jinsu1011/safenest-embedded-competition/docs/mmwave/MMWAVE_HANDOFF_NEXT.md

너는 SafeNest 프로젝트의 MR60BHA2 ESP 안정화 전담 엔지니어다.
전임자로부터 인수인계 받아 즉시 이어간다. 파일 읽고 확인해라, 임의 해석 금지.

════════════════════════════════════════════════
0. 사용자(김진수, 조장) 규칙
════════════════════════════════════════════════
- 항상 존댓말.
- "오늘은 여기까지" 같은 임의 종료 답변 금지.
- 옵션 나열보다 하나의 다음 행동을 명확히 제시.
- 사용자 "쉼" = 대기 (하드웨어·프로세스 유지). "ㄱㄱ" = 재개.
- 사용자 "잠시만" / "중지" = 백그라운드 프로세스 즉시 kill.
- 토큰 절약 요청 자주 함. 장황한 옵션 나열 금지.
- 로그 파일명 날짜 규칙은 2026-07-26을 계속 사용 중.

════════════════════════════════════════════════
1. 프로젝트
════════════════════════════════════════════════
SafeNest = 라즈베리파이 5 + MR60BHA2(mmWave) + Thermal-44(열화상) + SCD40(CO2) + PIR 융합
밀폐공간·차량 정지 인체와 위험 상태 감지, 프라이버시 보호 엣지 AI.

역할 분리 (넘지 말 것):
- ESP-WROOM-32: MR60 UART 수집, 유효성 판정, 최소 필터, raw+filtered 패킷화 → Pi 전송
- Raspberry Pi 5: 4센서 융합, 위험도 R, AI, SQLite, 대시보드, 경보
- 파이프라인·AI 학습·모델 반입 = 팀원 한준우 담당
- ESP에서 최종 정상/주의/위험 판정 금지 (Pi가 함)
- 내 담당 = mmWave 수집·검증·CSV 변환·통합 감독·발표

팀원 4명: 강유나(대시보드/PIR), 김태균(열화상), 유승하(SCD40/배선), 한준우(mmWave AI/융합).

════════════════════════════════════════════════
2. 두 대회 데드라인
════════════════════════════════════════════════
1) 창의혁신공모전 - 중간 2등 통과 확정. 최종보고서 2026-10-02, 최종발표 2026-10-16.
2) 임베디드SW경진대회 - 예선 마감 **2026-09-03**.
   - 필수: 개발완료보고서 PPT 20p PDF + GitHub Public + YouTube 3분 720p.
   - 팀명 후보 SANDI, 저장소명 2026ESWContest_free_<팀명>.

════════════════════════════════════════════════
3. 하드웨어 (변경 금지)
════════════════════════════════════════════════
ESP-WROOM-32 DevKit, PlatformIO esp32dev, ESP32-D0WD-V3 rev3.1, 4MB flash.
MR60BHA2 배선:
  5V → VIN/5V, GND → GND, MR60 TX → ESP GPIO16/RX2, MR60 RX → ESP GPIO17/TX2
UART 115200bps. RX0/TX0 금지. USB 하나 급전, 별도 5V 금지.

Mac 포트 (재연결마다 바뀜): find /dev -maxdepth 1 -name 'cu.usb*' -print
직전 포트: /dev/cu.usbserial-10  (capture_serial.py 기본값도 이 값)

Python venv: devices/mmwave/firmware/.venv/bin/python
설치됨: pyserial 3.5, rich 15.0.0

════════════════════════════════════════════════
4. 작업 폴더와 문서
════════════════════════════════════════════════
CWD: /Users/kimjinsu/Documents/임베디드 소프트웨어 경진대회

먼저 읽어라 (순서):
1. PROJECT_PROGRESS.md ← 최신 항목까지 반드시 다 읽어
2. MMWAVE_HANDOFF.md
3. HARDWARE_RUNBOOK.md
4. MMWAVE_TUNING.md
5. TEAM_OPERATING_MODEL.md

한준우 v3 배포본 (스펙 참고):
- /Users/kimjinsu/Downloads/SafeNest_team_distribution_20260725_v3/
- current/walkthrough/P0-6_mmwave_input_adapter.md
- models/mmwave_sensor_stats_metadata_v0.1.0.json

펌웨어 소스: devices/mmwave/firmware/src/main.cpp
  프레임 타입: 0x0A13 위상 / 0x0A14 호흡 / 0x0A15 심박 / 0x0A16 거리 / 0x0F09 재실 / 0xFFFF 펌웨어
  → 전부 스칼라 1개 값. 타깃 배열·인덱스 없음 = 단일 타깃 센서.

════════════════════════════════════════════════
5. 스크립트 (devices/mmwave/firmware/)
════════════════════════════════════════════════
- capture_serial.py       무필터 JSONL 캡처 (--port --baud --duration --output)
- analyze_mmwave_log.py   통계 리포트
- mmwave_dashboard.py     실시간 5Hz TUI
- aim_check.py            조준용 rolling presence
- entry_exit_trial.py     진입퇴장 자동 (완료, 재실행 불필요)
- analyze_entry_exit.py   진입퇴장 KPI 분석
- breath_pace_capture.py  메트로놈 페이싱
  **반드시 --explicit-phases 사용** (Tink=들이쉬기, 반주기 Pop=내쉬기).
  옵션 없이 쓰면 피험자가 Tink를 들이쉬기 전용으로 해석해 절반 호흡이 됨 (07-25 실패 원인).
  cue 레코드는 kind="cue", host_monotonic_ns(맥 시계) 사용.
  센서 레코드는 ts_monotonic_ms(ESP 시계). **시계가 다르므로 파일 기록 순서로 정렬할 것.**
- export_mmwave_csv.py    한준우 스펙 CSV 변환기

로그: logs/{baseline,matrix,kpi,breath,diagnostics,final,transitions}/
분석: analysis/{baseline,matrix,kpi,breath,diagnostics}/
1차 CSV 배치: csv/2026-07-25_han_junwoo_delivery/

로그 스키마 주의:
- 07-25 파일 = schema 1.0. human_detected_stable / heart_raw_valid / breath_raw_valid 필드 **없음**.
  → 재실은 human_detected_raw, 유효성은 값>0으로 판정할 것. 필드명 그대로 읽으면 전부 0%로 나온다.
- 07-26 파일 = schema 1.1. 위 필드 존재.

════════════════════════════════════════════════
6. 완료된 데이터 — 재측정 필요 없음
════════════════════════════════════════════════

### 2026-07-25 완료분
- logs/baseline/2026-07-25_empty_gate_v1_360s.jsonl
  빈 공간 6분 3598샘플, 재실 0.0%, 심박신호 0.0%, 호흡신호 0.0%. 오탐 KPI 만족.
- logs/baseline/2026-07-25_occupied_d09_v1_360s.jsonl
  90cm 인체 6분, 재실 100%, 심박신호 100%, 호흡신호 92.4%.
- logs/matrix/2026-07-25_occupied_d{06,12,15}_v1_360s.jsonl
  60cm→74.62cm 재실100% / 120cm→132.02cm 81.4% / 150cm→183.68cm 88.0%
  ※ 150cm의 breath 15.0·heart 87.0 std=0은 거리 문제가 아니라 lock-loss 고착이었음 (07-26 규명, 아래 참조)
- logs/kpi/2026-07-25_entry_exit_10.jsonl
  진입퇴장 10/10 통과, 평균 0.274초, 최악 0.642초 (PDF ≤2s 대비 여유). 해제 지연 평균 15.9초.
- logs/breath/2026-07-25_breath_paced_12rpm.jsonl
  ※ 절반 호흡 사고. 실제 흉부 주기 6.06rpm. 목표 12rpm 검증점으로 쓰지 말 것.
    다만 위상 알고리즘 재현성 확인용으로는 유효 (30초 창 median 6.00, std 0.48).

### 2026-07-26 완료분 (오늘)
- logs/kpi/2026-07-26_heartrate_ref_applewatch_300s.jsonl (1차)
  **150초 lock-loss freeze 발생.** 거리 149.24cm 고정(std=0.00), 심박신호 0%,
  그런데 human_detected_stable은 계속 true. 피험자는 실제로 80~86cm에 착석 중이었음.
  → ESP 유효성 로직의 핵심 근거 데이터. 폐기 금지.
- logs/kpi/2026-07-26_heartrate_ref_applewatch_run2_300s.jsonl (2차, 정상)
  90cm 5분 2998샘플, 재실 94.6%, 심박신호 94.2%, 호흡신호 88.8%.
  애플워치 10포인트 비교: MAE 10.65bpm, bias +6.35, 최대 32, r≈0 (추종 없음).
  필터 창 키워도 개선 안 됨. 상수 예측(MAE≈2.7)보다 나쁨 → 심박 절대값 사용 불가 확정.
- logs/breath/2026-07-26_breath_paced_15rpm.jsonl
  메트로놈 2.0001±0.0025s. 호흡신호 유효 100%. breath_phase std=0.3454.
  MR60 내장 breath_rate_raw = 18.03 (목표 15, +3.03 오차, ±2rpm 13.9%) → 내장값 불신 확정.
  위상 기반 추정 = 15.00rpm, ±2rpm 100%.
- logs/breath/2026-07-26_breath_paced_20rpm.jsonl (얕은 호흡, 실패 사례)
  breath_phase std=0.1134, 호흡유효 81.2%, ±2rpm 48.4%.
  원인은 "얕고 일정하게"라는 지시. **진폭 게이트 임계 근거로 보존. 폐기 금지.**
- logs/breath/2026-07-26_breath_paced_20rpm_deep.jsonl (깊은 호흡, 성공)
  breath_phase std=0.5007, 호흡유효 100%, ±2rpm 100% (영교차 창20s).

════════════════════════════════════════════════
7. 2026-07-26 확정된 설계 결정 (재논의 금지, 근거 위에 있음)
════════════════════════════════════════════════

### 7-1. 호흡 — ESP 최소 필터 확정
- **추정기: breath_phase 영교차 + 히스테리시스(진폭의 15%), 창 30초.**
  ±2rpm 통과율 15rpm 100% / 20rpm 100%. 연산 O(n)이라 ESP32에 적합.
- 자기상관 방식도 동등 성능이나 **옥타브(서브하모닉) 오류 주의**.
  탐색 범위에 2배 주기가 들어가면 반토막 값에 락함(20rpm에서 6.0s 락 실제 발생).
  쓰려면 "임계 이상인 가장 짧은 주기" 규칙 필수. 교차검증용으로만 유지.
- **진폭 게이트: breath_phase std < 0.2 → DEGRADED, 호흡수 미출력.**
  근거: 0.11 실패 / 0.35·0.50 통과.
- MR60 내장 breath_rate_raw는 원값 전송하되 **불신 표기**.
  오차가 일정하지 않음(6rpm에서 6.05 정확, 15rpm에서 +3.03) → 고정 보정 불가.

### 7-2. 심박 — 용도 확정
- **bpm 절대값 사용 금지.** MAE 10.65, r≈0. 정확도 KPI 보고서에서 제외.
- **용도는 "생체신호 유무" 채널.** 빈공간 0.0% vs 인체 94~100%로 완전 분리.
  정지 인체 판별의 독립 근거 (PIR은 움직임 필요, 열화상은 시야 필요).
- **단방향 증거 규칙 (안전 필수)**:
  "심박신호 있음 → 사람 있음" ✅ / "심박신호 없음 → 사람 없음" ❌ 성립 안 함.
  lock-loss로 건강한 사람도 150초간 0이 나왔음. 재실 판정은 다른 채널이 유지해야 함.
- **심정지 검출 불가.** 정확히 "신호 없음" 방향이라 신뢰 불가 + 자체 촬영 금지.

### 7-3. freeze / DEGRADED 판정 조건
- **거리 std=0 AND 심박신호 무효 → DEGRADED.**
- std=0 단독 금지. 완전 정지한 정상 인체도 거리 양자화(5.74cm 스텝)로 std=0이 나옴
  (07-26 2차 캡처 120~270s 구간, 심박 유효 100%인 정상 상태).

### 7-4. 다중 인원
- MR60BHA2는 **단일 타깃 센서** (프레임 구조상 값 1개, 타깃 배열 없음).
- 2인 분리 측정 불가. 인원 수 카운트는 열화상(김태균) 담당.
- "최소 1명 생존" 판정은 2인에서도 유효하나 **검출률 유지 여부는 미검증**.

════════════════════════════════════════════════
8. 남은 태스크
════════════════════════════════════════════════

#1 대안 B — 심박 하강 추종 검증 (사용자 + 애플워치 필요, 약 10분)
   목적: 안정 상태에서 r≈0이 나온 게 "워치 값이 78~88로 거의 안 변해서 따라갈 변화가
         없었기 때문"인지, 진짜 추종 불가인지 판정.
   방법: 계단 오르내려 심박 올린 직후 90cm 정면 착석 → 300초 캡처.
         30초마다 Yuna 음성 체크 신호, 사용자는 폰에 메모 후 종료 시 10개 일괄 보고.
         (입력 동작이 lock-loss 유발했으므로 실시간 채팅 입력 금지)
   watchdog 스크립트 재사용 가능:
     /private/tmp/.../scratchpad/hr_watchdog.py (거리 std=0 AND 심박무효 감지 시 음성 경고)
   판정: 하강 곡선을 따라가면 심박이 위험도 R 입력으로 승격. 아니면 생체 유무 전용 확정.

#2 CSV 배치 v2 출력 + 한준우 전달 (사용자 이탈 가능, 5~10분)
   export_mmwave_csv.py에 --matrix-jsonl, --breath-jsonl 옵션 추가 필요.
   포함 세션: NORMAL_D06 / D09 / D12 / D15 + BREATH_PACED_12 / 15 / 20
   새 폴더: csv/2026-07-26_han_junwoo_delivery_v2/
   매니페스트: 원본 SHA256 + 세션별 진단 리포트 + 원본 JSONL 사본.
   전달 메시지에 반드시 포함할 것:
   - 12rpm 세션은 절반 호흡 사고이므로 실제 6rpm. 라벨 해석 주의.
   - 20rpm은 얕은/깊은 두 버전 존재. 얕은 쪽은 저진폭 실패 사례.
   - MR60 내장 breath_rate_raw 신뢰 불가, resp_phase 원값 사용 권장 (모델 설계와 일치).
   - 150cm 세션의 std=0은 거리 문제가 아니라 lock-loss였음.

#3 PROJECT_PROGRESS.md에 2026-07-26 결과 기록 (미완료)
   위 7절 설계 결정 전부 + 근거 수치 포함.

#4 ESP 펌웨어 구현 (제 단독, 코드) ← 다음 큰 덩어리
   현재 breath_rate_filtered 필드는 전 패킷에서 null.
   4-1. breath_rate_filtered = 영교차+히스테리시스, 창 30초
   4-2. 진폭 게이트 (breath_phase std < 0.2 → DEGRADED)
   4-3. freeze 검출 (거리 std=0 AND 심박 무효 → DEGRADED)
   4-4. 스키마 1.2 승격 + 검증 캡처 (이때만 사용자 잠깐 필요)

#5 2인 동시 검증 (팀원 1명 필요, 다음 팀 모임)
   2인 90cm 나란히 착석 5분 → 심박신호 검출률·거리 안정성을 1인과 비교.

#6 대회 산출물 mmWave 파트 (임베디드SW 예선 2026-09-03)
   PPT 20p PDF / GitHub Public / YouTube 3분 720p.

════════════════════════════════════════════════
9. 한준우 CSV 스펙 (계약 조항, 반드시 준수)
════════════════════════════════════════════════
CSV 열 순서 고정 (11개):
  timestamp_s, resp_phase, subject_id, session_id, presence, label,
  breath_rpm, range_m, quality, signal_source, device_id

절대 규칙:
- resp_phase = ESP breath_phase 원값. ×100, Z-Score, offset 제거, smoothing, 재샘플링 금지.
- timestamp_s = 세션 시작 0으로 리베이스한 실측 초. 실제 timestamp 보존, 임의 추가·삭제 금지.
- 서로 다른 세션 병합 금지.
- presence=0 구간에 resp_phase=0 임의 생성 금지.
- 진입퇴장 라벨 = PRESENCE_TRANSITION (Class 1 금지).
- 5분 안정 인체 = NORMAL (거리별 NORMAL_D06 등). 메트로놈 = BREATH_PACED_<bpm>.
- signal_source = MR60BHA2_breath_phase, device_id = safenest-node-01.
- 파일명: <원본stem>__<session_id>.csv
- 매니페스트 필수 (원본 SHA256 + 원본 JSONL 사본 동봉).

도메인 gap: ESP breath_phase std ≈ 0.02~0.5 vs 학습 도메인 resp_phase std ≈ 2.5.
원값 보존 후 팀원 어댑터가 alignment 처리하기로 결정.

Class 1 (RAPID_OR_ABNORMAL): 학습 데이터 없음. MMWAVE_CLASS_UNVERIFIED, DEGRADED 처리.
APNEA: 자체 촬영 금지. 공개 db_records만.

════════════════════════════════════════════════
10. macOS 음성 안내 규칙
════════════════════════════════════════════════
목소리: Yuna (한국어).
사운드: Glass=시작, Ping=워밍업/전환, Hero=완료, Tink=들이쉬기, Pop=내쉬기, Sosumi=경고.
카운트: for s in 5 4 3 2 1; do say -v Yuna "${s}초" & sleep 1; done

════════════════════════════════════════════════
11. 안전·설계 금지
════════════════════════════════════════════════
- 숨참기, 과호흡, 밀폐공간, 가스 주입 시험 금지
- 0/null/NaN/timeout을 정상 호흡·무호흡으로 변환 금지
- 신호가 약할 때 틀린 숫자를 정상값처럼 출력 금지 (DEGRADED로 표시)
- 환경 오탐을 긴 시간 필터로 숨기기 금지
- ESP에서 최종 판정 금지
- 승인 없이 MR60 펌웨어 업데이트 금지
- 원본 로그 수정 금지 (파생만)
- 한 번에 필터·임계값 하나만 변경 후 동일 원본으로 비교
- 같은 방법 두 번 실패 시 반복 금지 (다른 방법 기록)
- 피험자에게 호흡 지시할 때 "얕게"라고 하지 말 것. 신호 진폭이 무너져 KPI가 깨진다.
  올바른 지시: "가슴을 분명히 부풀렸다 꺼뜨리세요. 빠르되 얕지 않게."

════════════════════════════════════════════════
12. 재개 즉시 순서
════════════════════════════════════════════════
Step 1. 상태 확인
  find /dev -maxdepth 1 -name 'cu.usb*' -print
  PROJECT_PROGRESS.md 마지막 섹션 읽기
Step 2. 15초 healthcheck
  capture_serial.py 15초 → 약 150샘플(10Hz), 오류 0 확인
Step 3. 설치 재검증 (하드웨어 뽑았다 꽂았을 경우만)
  빈 공간 60초 캡처 → 재실 0% 확인
Step 4. 사용자에게 보고 후 태스크 #1(대안 B)부터 진행.
  워치 준비 여부 먼저 확인할 것.
