jinsu1011/safenest-embedded-competition/docs/mmwave/MMWAVE_MASTER.md

# SafeNest mmWave 총정리 (2026-08-01 기준)

이 문서 하나로 인수인계가 끝나도록 작성했다. 다른 문서를 안 읽어도 이어서 작업할 수 있다.
`MMWAVE_HANDOFF_NEXT.md`와 내용이 겹치면 **이 문서가 우선**한다.

---

## 1. 프로젝트가 뭔가

**SafeNest** = 밀폐공간·정지 차량 안에서 **의식을 잃고 움직이지 않는 사람**을 찾아내는 엣지 AI 장치.
카메라를 쓰지 않아 프라이버시를 보호하는 것이 정체성이다.

센서 4종을 융합한다.

| 센서 | 역할 | 담당 |
|---|---|---|
| **MR60BHA2 (mmWave)** | 정지 인체의 호흡·생체신호 | **김진수 (나)** |
| Thermal-44 (열화상) | 인원 수·위치 | 김태균 |
| SCD40 (CO2) | 공간 환경 위험 | 유승하 |
| PIR | 움직임 | 강유나 |
| 융합·AI·대시보드 | 위험도 R 산출 | 한준우, 강유나 |

연산은 **Raspberry Pi 5**에서, 센서 수집은 **ESP-WROOM-32**에서 한다.

### 왜 mmWave가 핵심인가
움직이는 사람은 PIR로도 잡는다. 문제는 **쓰러져서 안 움직이는 사람**이다.
- PIR → 움직여야 감지. 못 잡음.
- 열화상 → 담요·시트·시야 가림에 약함.
- CO2 → 공간 전체 값이라 개인 특정 불가.
- **mmWave → 정지해 있어도 흉부의 호흡 미세 움직임을 잡는다.**

즉 mmWave가 이 프로젝트에서 **가장 어려운 문제를 맡은 센서**다.

### 역할 경계 (넘지 말 것)
- **ESP-WROOM-32**: MR60 UART 수집 → 유효성 판정 → 최소 필터 → raw+filtered 패킷화 → Pi 전송
- **Raspberry Pi 5**: 4센서 융합, 위험도 R, AI 추론, SQLite, 대시보드, 경보
- **ESP에서 "정상/주의/위험" 최종 판정 금지.** 판정은 Pi가 한다.
- AI 학습·모델 반입은 한준우 담당. 내가 하지 않는다.
- 내 담당 = mmWave 수집·검증·CSV 변환·통합 감독·발표

---

## 2. 하드웨어와 실행 환경

```
ESP-WROOM-32 DevKit (ESP32-D0WD-V3 rev3.1, 4MB flash, PlatformIO esp32dev)
MR60BHA2 배선:
  5V  → VIN/5V
  GND → GND
  MR60 TX → ESP GPIO16 (RX2)
  MR60 RX → ESP GPIO17 (TX2)
UART 115200bps. RX0/TX0 사용 금지. USB 하나로 급전, 별도 5V 금지.
```

- 작업 폴더: `/Users/kimjinsu/Documents/임베디드 소프트웨어 경진대회`
- GitHub: `jinsu1011/safenest-embedded-competition` (**private**), 브랜치 `codex/mmwave-phase-integration`
- Python: `devices/mmwave/firmware/.venv/bin/python` (pyserial, rich)
- 시리얼 포트는 **재연결마다 바뀐다**: `find /dev -maxdepth 1 -name 'cu.usb*' -print`
  - 최근 값 `/dev/cu.usbserial-10`
- 펌웨어 소스: `devices/mmwave/firmware/src/main.cpp`
- 샘플레이트 약 **10Hz**

### MR60BHA2 UART 프레임 (main.cpp:15~21)
`0x0A13` 위상 / `0x0A14` 호흡수 / `0x0A15` 심박수 / `0x0A16` 거리 / `0x0F09` 재실 / `0xFFFF` 펌웨어

**전부 값 1개짜리 스칼라다. 타깃 배열도 인덱스도 없다 → 단일 타깃 센서.**

---

## 3. 지금까지 한 것 (전부 완료, 재측정 불필요)

원본 로그는 전부 `devices/mmwave/firmware/logs/` 에 있고 GitHub에 푸시돼 있다.
**원본 수정 금지. 파생 파일만 만든다.**

### 3-1. 환경 검증
| 세션 | 파일 | 결과 |
|---|---|---|
| 빈 공간 6분 | `baseline/2026-07-25_empty_gate_v1_360s.jsonl` | 3598샘플, 재실 **0.0%**, 심박신호 0.0%, 호흡신호 0.0% → 오탐 KPI 통과 |
| 90cm 인체 6분 | `baseline/2026-07-25_occupied_d09_v1_360s.jsonl` | 재실 100%, 심박신호 100%, 호흡신호 92.4% |

### 3-2. 거리 매트릭스
`matrix/2026-07-25_occupied_d{06,12,15}_v1_360s.jsonl`

| 안내 거리 | 실측 | 재실 | 판정 |
|---|---|-----|-----|
| 60cm | 74.62cm | 100% | 최적 |
| 90cm | 97.58cm | 100% | 최적 |
| 120cm | 132.02cm | 81.4% | KPI 미달 |
| 150cm | 183.68cm | 88.0% | 측정 실패 |

**최적 흉부 거리 = 60~100cm.**
※ 150cm의 `std=0` 상수값은 원래 "거리가 멀어 실패"로 기록됐으나, 2026-08-01에 **거리 문제가 아니라 lock-loss 고착**임이 밝혀졌다 (5-3 참조).

### 3-3. 진입/퇴장 KPI — 통과
`kpi/2026-07-25_entry_exit_10.jsonl` (센서 4215 + 비프 20)
- **감지 10/10 통과. 평균 0.274초, 최악 0.642초** (요구 ≤2초 대비 3배 여유)
- 해제 지연은 평균 15.9초 (MR60 hysteresis 추정, 우선순위 낮음)

### 3-4. 심박 정확도 대조 (애플워치 기준) — 2026-08-01
| 파일 | 내용 |
|---|---|
| `kpi/2026-07-26_heartrate_ref_applewatch_300s.jsonl` | 1차. **150초 lock-loss freeze 발생** |
| `kpi/2026-07-26_heartrate_ref_applewatch_run2_300s.jsonl` | 2차. 정상. 2998샘플, 재실 94.6%, 심박신호 94.2%, 호흡신호 88.8% |

2차에서 워치 10포인트와 대조한 결과:
- **MAE 10.65bpm, bias +6.35, 최대 오차 32bpm, 상관계수 r ≈ 0**
- 중앙값 필터 창을 ±5s→±45s로 9배 키워도 bias는 +6.35→+5.00으로 거의 안 줄었다.
- 워치 std가 3.38이라 **"그냥 평균값 79.6을 상수로 찍는 예측"의 MAE가 약 2.7**이다.
  MR60을 필터링하고 오프셋 보정해도 **4.20** — **아무것도 안 재는 것보다 나쁘다.**
- → **심박 bpm 절대값은 회귀·보정·캘리브레이션으로 못 살린다. 확정.**

### 3-5. 메트로놈 호흡 시험 — 2026-08-01
`breath_pace_capture.py --explicit-phases` 사용 (Tink=들이쉬기, 반주기 Pop=내쉬기).

| 파일 | 목표 | breath_phase 진폭(std) | 호흡유효 | 비고 |
|---|-----|---|---|---|
| `breath/2026-07-25_breath_paced_12rpm.jsonl` | 12rpm | — | 67.8% | **절반 호흡 사고. 실제 6.06rpm** |
| `breath/2026-07-26_breath_paced_15rpm.jsonl` | 15rpm | **0.3454** | 100% | 성공 |
| `breath/2026-07-26_breath_paced_20rpm.jsonl` | 20rpm | **0.1134** | 81.2% | **얕은 호흡 실패 사례** |
| `breath/2026-07-26_breath_paced_20rpm_deep.jsonl` | 20rpm | **0.5007** | 100% | 성공 |

메트로놈 자체 정확도는 완벽했다 (15rpm에서 2.0001±0.0025초).

---

## 4. 확정된 설계 결정 — **재논의 금지, 근거는 위 데이터**

### 4-1. 호흡 — ESP 최소 필터 (핵심 성과)

**MR60 내장 `breath_rate_raw`를 버리고, `breath_phase` 원신호에서 직접 호흡수를 계산한다.**

`breath_phase` 자기상관으로 실제 흉부 주기를 재보니 메트로놈과 정확히 일치했다.
즉 **원신호는 정확한데 MR60의 내장 추정기가 틀린다.**

| 추정 방식 | 15rpm | 20rpm(깊은) | 결과 |
|---|---|---|---|
| MR60 내장 breath_rate_raw | 18.03 (오차 +3.03) | — | **±2rpm 통과율 13.9%** |
| **영교차 + 히스테리시스, 창 30초** | 15.30 | 20.17 | **±2rpm 100% / 100%** |
| 자기상관 + 옥타브 보정, 창 30초 | 14.96 | 19.97 | ±2rpm 100% / 99.3% |

**채택: 영교차 + 히스테리시스(진폭의 15%), 창 30초.**
연산량이 O(n)이라 ESP32에 적합하다. 자기상관은 동등 성능이지만 수십 배 무겁고 옥타브 오류 위험이 있어 교차검증용으로만 남긴다.

**진폭 게이트: `breath_phase` std < 0.2 → DEGRADED, 호흡수 미출력.**
근거: 0.11에서 실패(±2rpm 48.4%), 0.35·0.50에서 통과(100%).
신호가 약할 때 틀린 숫자를 정상값처럼 내보내는 것은 안전 규칙 위반이다.

**MR60 내장값은 원값 그대로 전송하되 "불신" 표기.**
오차가 일정하지 않다 — 6rpm에서는 6.05로 정확했는데 15rpm에서는 +3.03이었다. **고정 오프셋 보정이 불가능하다.**

### 4-2. 심박 — 용도 재정의

**bpm 절대값 사용 금지.** 보고서에서 심박 정확도 KPI를 뺀다.

**대신 "생체신호 유무" 채널로 쓴다.** 이건 데이터로 완전히 증명됐다.

| 세션 | 심박신호 검출률 |
|---|---|
| 빈 공간 6분 (3598샘플) | **0.0%** |
| 인체 90cm (2026-07-25) | **100.0%** |
| 인체 90cm (2026-08-01) | **94.2%** |

무인 3598샘플에서 오탐 **0건**. 완전히 분리된다.
→ **정지한 사람을 찾아내는 독립 근거**로 쓴다. 프로젝트 주제와 정확히 맞는 역할이다.

#### ⚠️ 단방향 증거 규칙 (안전 필수, 반드시 지킬 것)
- **"심박신호 있음 → 사람 있음"** ✅ 성립
- **"심박신호 없음 → 사람 없음"** ❌ **성립하지 않는다**

1차 캡처에서 **건강한 사람이 앉아 있는데도 150초 동안 신호가 0**이었다 (lock-loss).
이 방향으로 판정하면 사람을 놓친다. **재실 판정은 거리·호흡·PIR·열화상이 유지해야 한다.**

같은 이유로 **심정지 검출은 불가능하다.** 심정지는 정확히 "신호 없음" 방향인데, 그게 우리가 신뢰할 수 없다고 증명한 유일한 방향이다. 게다가 심정지는 자체 촬영이 금지돼 검증 데이터를 만들 수도 없다.

### 4-3. freeze / DEGRADED 판정

**조건: 거리 std=0 AND 심박신호 무효 — 두 개 동시 성립.**

`std=0` 단독으로 걸면 안 된다. 완전히 정지한 **정상** 인체도 거리 양자화(5.74cm 스텝) 때문에 std=0이 나온다 (2026-08-01 2차 캡처 120~270초 구간, 심박 유효 100%인 정상 상태).

### 4-4. 다중 인원

**MR60BHA2는 단일 타깃 센서다** (프레임이 전부 스칼라 1개, 타깃 배열 없음).
- 2인 분리 측정 불가. 사람별 개별 심박·호흡 불가. 인원 수 카운트 불가.
- **인원 수는 열화상(김태균)이 담당** — 설계상 이미 역할이 분리돼 있어 구멍이 아니다.
- "최소 1명 생존" 판정은 2인에서도 성립하나, **검출률이 유지되는지는 미검증** (남은 작업 #5).

---

## 5. 겪은 실패와 함정 — **같은 실수 반복 금지**

### 5-1. 절반 호흡 사고 (2026-07-25 12rpm)
메트로놈은 완벽했는데 센서가 5.63rpm을 읽었다. 목표 12rpm의 정확히 절반이었다.
원인은 센서가 아니라 **신호 해석**이었다. Tink를 "들이쉬기 신호"로만 듣고 다음 Tink에 내쉬어서 한 호흡에 10초를 썼다.
→ **`breath_pace_capture.py`는 반드시 `--explicit-phases`로 실행할 것.** (Tink=들이쉬기, 반주기 Pop=내쉬기)
→ 12rpm 세션은 **실제 6.06rpm**이므로 12rpm 검증점으로 쓰면 안 된다.

### 5-2. "얕게 쉬세요"라는 지시가 KPI를 깨뜨림
20rpm 1차에서 내가 "얕고 일정하게"라고 지시했다. 얕게 쉬면 흉부 변위가 작아져 신호 진폭이 0.1134까지 떨어졌고(정상 0.35~0.50) KPI가 48.4%로 무너졌다.
같은 20rpm을 **"가슴을 분명히 부풀렸다 꺼뜨리세요"** 로 다시 찍으니 진폭 0.5007, KPI 100%가 나왔다.
→ **피험자에게 "얕게"라고 지시하지 말 것.** 올바른 지시: "빠르되 얕지 않게, 가슴이 분명히 움직이게."

### 5-3. lock-loss freeze — 거리 문제가 아니었다
1차 심박 캡처에서 30초~180초 동안 거리가 **149.24cm에 완전 고정(std=0.00)**, 심박신호 0%였다. 피험자는 계속 80~86cm에 앉아 있었다.
이것은 2026-07-25 "150cm 측정 실패"와 **동일한 시그니처**다. 즉 **거리와 무관한 lock-loss 고착**이다. 어제 결론이 틀렸다.
더 심각한 건 그 150초 동안 `human_detected_stable`이 계속 **true**였다는 점이다 — ESP가 쓰레기 값을 재실 YES로 Pi에 넘긴다.
→ 이것이 4-3 판정 로직이 필요한 이유다. **이 로그는 폐기 금지.**
→ 움직임(채팅 입력)이 방아쇠로 추정된다. 캡처 중 피험자가 타이핑하지 않게 할 것.

### 5-4. 자기상관 옥타브(서브하모닉) 오류
20rpm에서 자기상관이 **6.000초(2배 주기)** 에 락해 10rpm을 출력했다. 실제는 3.0초/20rpm.
15rpm에서 통과한 건 알고리즘이 옳아서가 아니라 2배 주기 8.0초가 탐색 범위(상한 7.5초) 밖이라 **운이 좋았던 것**이다.
→ 자기상관을 쓸 거면 최대값이 아니라 **"임계(최대값의 85%) 이상인 가장 짧은 주기"** 를 골라야 한다.

### 5-5. 로그 스키마가 2종이다
- **2026-07-25 파일 = schema 1.0**: `human_detected_stable`, `heart_raw_valid`, `breath_raw_valid` 필드가 **없다**.
  그대로 읽으면 **전부 0%로 나온다**(실제로 한 번 잘못 계산했다). `human_detected_raw` + 값>0 으로 판정할 것.
- **2026-07-26 이후 = schema 1.1**: 위 필드 존재.

### 5-6. 시계가 2종이다
- cue 레코드(`kind="cue"`)는 `host_monotonic_ns` — **맥 시계**
- 센서 레코드는 `ts_monotonic_ms` — **ESP 시계**
- 서로 변환 불가. **파일에 기록된 순서로 정렬**해야 한다. `analysis_tools/`의 모든 스크립트가 이 방식을 쓴다.

---

## 6. 남은 작업 (우선순위 순)

| # | 작업 | 소요 | 사람 필요? | 하드웨어 필요? |
|---|---|---|---|---|
| 1 | **ESP 펌웨어 구현** | 큼 | 아니오 | 검증 때만 |
| 2 | CSV 배치 v2 + 한준우 전달 | 5~10분 | 아니오 | 아니오 |
| 3 | PROJECT_PROGRESS.md 기록 | 짧음 | 아니오 | 아니오 |
| 4 | 2026-07-28 로그 중복 확인 | 짧음 | 아니오 | 아니오 |
| 5 | 심박 하강 추종 검증 (선택) | 10분 | **예 + 애플워치** | 예 |
| 6 | 2인 동시 검증 | 10분 | **팀원 1명** | 예 |
| 7 | 대회 산출물 | 큼 | 팀 전체 | 일부 |

### #1 ESP 펌웨어 구현 ← **다음 큰 덩어리**
현재 `breath_rate_filtered` 필드는 **전 패킷에서 `null`** 이다. 설계만 확정됐고 코드가 없다.
1. `breath_rate_filtered` = breath_phase 영교차 + 히스테리시스(15%), 창 30초
2. 진폭 게이트: `breath_phase` std < 0.2 → DEGRADED
3. freeze 검출: 거리 std=0 AND 심박 무효 → DEGRADED
4. 패킷 스키마 **1.2**로 승격 + 검증 캡처 (이때만 사용자·하드웨어 필요)

참고 구현: `analysis_tools/phase_rate_zerocross.py` 의 `zc_rate()` 를 C++로 옮기면 된다.

### #2 CSV 배치 v2
`export_mmwave_csv.py`에 `--matrix-jsonl`, `--breath-jsonl` 옵션 추가 필요.
포함 세션: NORMAL_D06 / D09 / D12 / D15 + BREATH_PACED_12 / 15 / 20
출력 폴더: `csv/2026-07-26_han_junwoo_delivery_v2/`
매니페스트에 원본 SHA256 + 세션별 진단 + 원본 JSONL 사본 동봉.

**한준우에게 반드시 전달할 내용:**
- 12rpm 세션은 절반 호흡 사고라 **실제 6rpm**이다. 라벨 해석 주의.
- 20rpm은 얕은/깊은 두 버전이 있다. 얕은 쪽은 저진폭 실패 사례다.
- **MR60 내장 `breath_rate_raw`는 신뢰 불가.** `resp_phase` 원값을 쓰는 모델 설계가 옳다.
- 150cm 세션의 std=0은 거리 문제가 아니라 lock-loss였다.

### #4 2026-07-28 로그 중복 확인
`logs/breath/2026-07-28_breath_paced_*` 에 12rpm/15rpm explicit 재시도 로그가 있다.
내가 인수인계받지 못한 다른 세션의 작업이다. 2026-08-01 작업과 중복인지 확인하고 어느 쪽이 유효한지 정리할 것.

### #5 심박 하강 추종 검증 (선택)
안정 상태에서 r≈0이 나온 이유가 **워치 값이 78~88로 거의 안 변해 따라갈 변화가 없었기 때문**일 수 있다.
계단 운동으로 심박을 올린 뒤 90cm 착석 5분 캡처 → 110→80 하강 곡선을 MR60이 따라가는지 본다.
- 따라가면 → 심박이 위험도 R의 정식 입력으로 승격
- 아니면 → 생체 유무 전용으로 확정 (근거 2배)

**주의**: 캡처 중 피험자가 채팅에 타이핑하면 lock-loss가 유발된다(5-3). 폰에 메모했다가 끝나고 일괄 보고하게 할 것.
`analysis_tools/freeze_watchdog.py`를 동시에 돌리면 고착을 실시간 음성 경고해준다.

---

## 7. 대회 일정

| 대회 | 상태 | 마감 |
|---|---|---|
| 창의혁신공모전 | 중간 **2등 통과 확정** | 최종보고서 **2026-10-02** / 발표 **2026-10-16** |
| 임베디드SW경진대회 | 예선 준비 중 | **2026-09-03** |

**임베디드SW 예선 제출물 (필수 3종)**
1. 개발완료보고서 PPT 20페이지 → PDF
2. GitHub **Public** 저장소 (현재는 private) — 이름 규칙 `2026ESWContest_free_<팀명>`, 팀명 후보 **SANDI**
3. YouTube 3분 720p 영상

발표는 김진수(나) 담당.

---

## 8. 한준우 CSV 계약 스펙 (반드시 준수)

열 순서 고정 (11개):
```
timestamp_s, resp_phase, subject_id, session_id, presence, label,
breath_rpm, range_m, quality, signal_source, device_id
```

**절대 규칙**
- `resp_phase` = ESP `breath_phase` **원값**. ×100, Z-Score, offset 제거, smoothing, 재샘플링 **전부 금지**.
- `timestamp_s` = 세션 시작을 0으로 리베이스한 실측 초. 실제 timestamp 보존, 임의 추가·삭제 금지.
- 서로 다른 세션 **병합 금지**.
- `presence=0` 구간에 `resp_phase=0`을 임의 생성 금지 (원값 그대로).
- 라벨: 진입퇴장 = `PRESENCE_TRANSITION` (Class 1 금지) / 5분 안정 인체 = `NORMAL`(거리별 `NORMAL_D06` 등) / 메트로놈 = `BREATH_PACED_<bpm>`
- `signal_source` = `MR60BHA2_breath_phase`, `device_id` = `safenest-node-01`
- 파일명: `<원본stem>__<session_id>.csv`
- 매니페스트 필수 (원본 SHA256 + 원본 JSONL 사본 동봉)

**알려진 도메인 gap**: ESP `breath_phase` std ≈ 0.02~0.5 vs 학습 도메인 `resp_phase` std ≈ 2.5.
원값을 보존하고 **팀원 어댑터가 alignment를 처리**하기로 결정했다.

**Class 1 (RAPID_OR_ABNORMAL)**: 학습 데이터 없음 → `MMWAVE_CLASS_UNVERIFIED`, DEGRADED 처리.
**APNEA**: 자체 촬영 금지(안전 규칙). 공개 db_records만 사용.

---

## 9. 안전·설계 금지 사항

- 숨참기, 과호흡, 밀폐공간, 가스 주입 시험 **금지**
- 0/null/NaN/timeout을 정상 호흡이나 무호흡으로 변환 **금지**
- 신호가 약할 때 틀린 숫자를 정상값처럼 출력 **금지** (DEGRADED로 표시할 것)
- 환경 오탐을 긴 시간 필터로 숨기기 **금지**
- ESP에서 최종 판정 **금지**
- 승인 없이 MR60 펌웨어 업데이트 **금지**
- 원본 로그 수정 **금지** (파생 파일만)
- 한 번에 필터·임계값 **하나만** 변경 후 동일 원본으로 비교
- 같은 방법 두 번 실패하면 반복 금지 (다른 방법을 기록할 것)
- 피험자에게 **"얕게 쉬세요"라고 지시 금지** (5-2 참조)

---

## 10. 분석 도구 — `devices/mmwave/firmware/analysis_tools/`

하드웨어 없이 로그만으로 위 결론을 전부 재현할 수 있다. 표준 라이브러리만 쓴다.
자세한 사용법은 그 폴더의 `README.md`에 있다.

| 스크립트 | 용도 |
|---|---|
| `phase_rate_zerocross.py` | **ESP 채택 알고리즘.** 영교차+히스테리시스 |
| `phase_rate_autocorr_octave.py` | 자기상관 + 옥타브 보정 (교차검증) |
| `phase_rate_autocorr.py` | 옥타브 보정 없는 버전 (실패 재현용) |
| `phase_period.py` | 단일 세션 실제 호흡 주기 |
| `phase_any_session.py` | schema 1.0 구버전 로그용 |
| `vital_presence_discrim.py` | 빈공간 vs 인체 생체신호 판별력 |
| `hr_ref_compare.py` | 애플워치 대조 |
| `hr_window_sweep.py` | 중앙값 창 크기별 오차 |
| `hr_corr_bias.py` | 상관계수 + 오프셋 보정 |
| `session_bin_diag.py` | 30초 구간별 진단 (freeze 탐지) |
| `freeze_watchdog.py` | 실시간 freeze 음성 경고 (macOS) |
| `hr_ref_capture_run.sh` | 심박 대조 캡처 러너 (macOS) |

---

## 11. 바로 시작하는 법

### 11-0. 다른 컴퓨터에서 처음 받는 경우

저장소는 **private**이다. `jinsu1011` 계정으로 로그인돼 있거나 개인 액세스 토큰이 있어야 clone된다.

```bash
git clone -b codex/mmwave-phase-integration \
  https://github.com/jinsu1011/safenest-embedded-competition.git
cd safenest-embedded-competition
```

작업 브랜치는 `codex/mmwave-phase-integration`이다. `main`이 아니므로 `-b` 옵션을 빠뜨리지 말 것.

**Python 환경 재생성** (`.venv`는 `.gitignore`로 제외돼 저장소에 없다):

```bash
cd devices/mmwave/firmware
python3 -m venv .venv
.venv/bin/pip install pyserial rich
```

단, **`analysis_tools/`의 분석 스크립트는 표준 라이브러리만 쓰므로 venv 없이 `python3`로 바로 돌아간다.**
pyserial·rich는 실측 캡처(`capture_serial.py`, `breath_pace_capture.py`, `mmwave_dashboard.py`)에만 필요하다.

**저장소에 없어서 따로 챙겨야 하는 것**
- 한준우 v3 배포본 — `~/Downloads/SafeNest_team_distribution_20260725_v3/`
  (CSV 작업 #2의 스펙 참고용: `current/walkthrough/P0-6_mmwave_input_adapter.md`,
   `models/mmwave_sensor_stats_metadata_v0.1.0.json`)
- ESP + MR60BHA2 실물 (실측 캡처에만 필요)

**OS별 제약**
| 작업 | macOS | Windows/Linux |
|---|---|---|
| 분석 스크립트 (`analysis_tools/`) | ✅ | ✅ |
| 펌웨어 구현 (PlatformIO) | ✅ | ✅ |
| CSV 변환·문서 | ✅ | ✅ |
| 음성 안내 캡처 (`say`/`afplay` 사용) | ✅ | ❌ |
| 실측 캡처 | 하드웨어 필요 | 하드웨어 필요 |

**하드웨어 없이도 남은 작업 #1(펌웨어 구현), #2(CSV), #3(문서), #4(중복 확인)를 전부 진행할 수 있다.**
가장 큰 덩어리인 #1이 하드웨어 없이 가능하다.

### 11-1. 하드웨어가 있는 경우 (기존 맥 기준)

```bash
cd "/Users/kimjinsu/Documents/임베디드 소프트웨어 경진대회"
find /dev -maxdepth 1 -name 'cu.usb*' -print          # 포트 확인 (매번 바뀜)

# 15초 healthcheck — 약 150샘플(10Hz), 오류 0이면 정상
devices/mmwave/firmware/.venv/bin/python \
  devices/mmwave/firmware/capture_serial.py \
  --port /dev/cu.usbserial-10 --duration 15 --output /tmp/hc.jsonl
```

하드웨어를 뽑았다 다시 꽂았으면 빈 공간 60초 캡처로 재실 0%를 확인한 뒤 진행한다.
위치가 그대로면 생략해도 된다.

**하드웨어 없이 이어받는 경우**: 작업 #1(펌웨어 구현), #2(CSV), #3(문서), #4(중복 확인)는 전부 진행 가능하다.

---

## 12. 알려진 미해결 이슈

1. **파일명 날짜 불일치** — 2026-08-01에 캡처한 로그가 인수인계 지시에 따라 `2026-07-26`으로 명명돼 있다.
   원본 파일명을 바꾸면 기존 분석·매니페스트 참조가 깨지므로, **파일명은 두고 `PROJECT_PROGRESS.md`에 실제 캡처일을 병기**할 것을 권장한다.
2. **2026-07-28 세션 로그** — 다른 세션의 작업이 함께 커밋돼 있다. 중복 여부 미확인 (작업 #4).
3. **해제 지연 15.9초** — 진입 감지는 0.274초로 우수하나 퇴장 후 해제가 느리다. 우선순위 낮음.
4. **저장소가 private** — 대회 제출은 Public + 이름 규칙 `2026ESWContest_free_<팀명>` 필요.
