jinsu1011/safenest-embedded-competition/final-report/docs/00_SUBMISSION_REQUIREMENTS.md

# 00_SUBMISSION_REQUIREMENTS

제24회 임베디드SW경진대회 (2026) · 자유공모 부문
Team: 가만있어도SANDI · Project: SafeNest

Source of truth for this file:

- `00_Official/01_2026_개발완료보고서_작성안내.pdf` (사무국, 2026-05-06)
- `00_Official/02_2026_자유공모_세부안내.pdf` (2026.05)
- `00_Official/03_2026_임베디드SW경진대회_규정.pdf` (2026.05)

All statements below are transcribed/derived from those three documents only.
Status values: **PASS** / **MISSING** / **NOT VERIFIED**.

---

## 1. PRELIMINARY SUBMISSION (예선 제출물)

Official table (자유공모 세부안내 p.4, "나. 제출서류") — 예선 4 items, all via 구글폼 except where noted.

| # | 제출 서류 | 분량 | 파일타입 | 공식 파일명 / 제목 규칙 | 업로드 위치 | STATUS |
|---|---|---|---|---|---|---|
| 1 | 참가신청서 | 1 page | 엑셀 | `2026ESWContest_자유공모_가만있어도SANDI_참가신청서` | 구글폼 | **NOT VERIFIED** — 패키지 내 없음 (자동생성 서류) |
| 2 | 개발완료보고서(PPT) | 20page 이내 | **PDF** | `2026ESWContest_자유공모_가만있어도SANDI_개발완료보고서` | 구글폼 | **본 작업 산출물 (DRAFT)** |
| 3 | 소스코드 | - | - | `github.com/사용자이름/2026ESWContest_free_가만있어도SANDI` | GitHub | **MISSING (naming noncompliant)** — §4 참조 |
| 4 | 시연동영상 | 3분 이내 | - | `2026ESWContest_자유공모_가만있어도SANDI_시연동영상` | YouTube | **MISSING** — §5 참조 |

- 예선접수 마감: **~9월 3일(목)** (자유공모 세부안내 p.3 "나. 예선접수")
- ※ 공식 주의: "서류 제출 시 주최 측이 제시한 양식 및 기간을 준수하지 않을 경우 불이익(감점, 심사 대상 제외, 장비 지급 불가 등)이 있을 수 있음"
- 소스코드·시연동영상 링크는 **개발완료보고서에 반드시 삽입**해야 함 (양 공식문서 모두 "필수" 명시).

## 2. DEVELOPMENT COMPLETION REPORT (개발완료보고서)

### 2.1 형식

| 요구사항 | 공식 근거 | STATUS |
|---|---|---|
| PPT 등으로 작업 후 **반드시 PDF로 변환하여 제출** | 작성안내 p.1 항목1 | 계획 준수 (PPTX → PDF) |
| 필수 항목 포함, **양식은 자유** | 작성안내 p.1 항목3 | PASS |
| 내용 추가/디자인 자유 | 작성안내 p.1 항목3 | PASS |
| **최대 20p 초과 금지 — 표지 및 인사 페이지(Thank you 등) 제외** | 작성안내 p.1 항목3 | 계획: 표지 1 + 콘텐츠 20 = 21 슬라이드 |
| 표지 제외 20P **초과분은 평가 시 미반영** | 자유공모 세부안내 p.4 각주 | 20p 엄수 |
| 저작권 문제 없는 **서체 및 이미지** 사용 권장, 책임은 참가팀 | 작성안내 p.1 항목2 | §6 참조 |

### 2.2 필수 7개 항목 및 공식 분량

| No. | 필수 항목 | 분량 |
|---|---|---|
| 1 | 개발 개요(프로젝트 개발 배경, 동기, 목표, 필요성 등) **+ 소스코드 및 시연동영상 링크(필수)** | **3P** |
| 2 | 개발 환경 설명 (HW 구성 및 기능, SW구성, 기능 설계도, 개발 환경 등) | |
| 3 | 개발 프로그램 설명 (파일 구성, 함수별 기능, 흐름도, 기술적 차별성) | **10P** |
| 4 | 개발 중 발생한 장애요인과 해결방안 | |
| 5 | 개발 결과물의 차별성(작품의 차별성 및 우수성 설명) | **5P** |
| 6 | 개발 결과물의 파급력 및 기대효과(판매가치, 시장성, 활용성, 발전 가능성 등) | |
| 7 | 개발 일정 및 업무 분장 | **2P** |

- 항목 3-1 "(스마트 가전 부문) 가산점 항목" → **자유공모 부문에는 해당 없음**.
- ※ "필수항목별 분량의 일부 조정은 허용" (자유공모 세부안내 p.4).
- 채택 배분: **3 + 10 + 5 + 2 = 20P**.

### 2.3 표지 (작성안내 "예시" 페이지)

```
제24회 임베디드SW경진대회 개발완료보고서
<부문>
<작품명>
<팀번호_팀명>
```
→ 팀번호는 패키지 내 어디에도 없음. **NOT VERIFIED** → `[팀번호 확인 필요]_가만있어도SANDI` 사용, 날조 금지.

### 2.4 항목 7 작성 지시 (작성안내 예시 페이지)

- ※ **실제 프로젝트 개발 일정** 작성
- ※ 프로젝트 개발 관련 **팀원의 업무 분장 위주**로 작성
- 예시 양식: 좌측 월별 일정표(내용/주차), 우측 구분·성명·업무분장 표 + 팀장/팀원 담당업무 카드.

## 3. JUDGING CRITERIA (심사 항목) — 자유공모 세부안내 p.5 "다. 심사 항목 안내"

예선/결선 공통 배점.

| 구분 | 배점 | 항목별 설명 (원문) |
|---|---:|---|
| 독창성 | **30** | 적절한 개발 동기 및 배경설명 / 작품의 독창적인 아이디어 / 기존 제품 또는 유사제품과의 차별성 |
| 기술성 및 완성도 | **30** | 기술적 독창성 및 난이도 정도 / 작품의 기술적 완성도 및 구현 여부 / **임베디드SW기술 적용 여부** |
| 활용성 | **20** | 작품의 기대효과 및 파급성 / 추후 발전 가능성 |
| 정보전달력 | **10** | 프로젝트에 대한 문서 완성도 및 정보전달 |
| 팀 구성 및 팀 역량 | **10** | 작품 개발을 위한 팀 구성 및 역할 배분 적절성 |

- 독창성 + 기술성/완성도 = **60/100**. 기술 증거와 차별성 페이지가 보고서를 지배해야 함.
- 심사방식: 예선은 **서류심사** — 제출 서류만으로 심사됨 (구두 보충 기회 없음). 정보전달력 10점이 실질적으로 전 항목 전달 효율을 좌우.
- 규정 제15조 ③: 심사위원 점수 중 **최고/최저 제외 후 합산**.

## 4. SOURCE CODE (소스코드)

| 요구사항 | 공식 근거 | 현재 상태 | STATUS |
|---|---|---|---|
| GitHub 주소 제출 | 세부안내 p.4 | `https://github.com/jinsu1011/safenest-embedded-competition` | 존재 |
| 명명 규칙 `github.com/사용자이름/2026ESWContest_free_팀명` | 세부안내 p.4 | 현재 repo명 `safenest-embedded-competition` | **MISSING / NONCOMPLIANT** |
| 개발완료보고서에 해당 링크 삽입 | 세부안내 p.4 | DRAFT에 실제 URL 삽입 예정 | 계획 |
| 수상작은 GitHub 공개범위 **Public 유지** (임의 Private 전환 시 수상 철회 가능) | 세부안내 p.6 "5-마" | 공개 상태 미확인 | **NOT VERIFIED** |
| 오픈소스 포함 시 **해당 라이선스 규정 위반 금지** (수상작 아니어도 전 참가팀 해당) | 세부안내 p.6 "5-라" | 스냅샷 라이선스 감사 필요 | **NOT VERIFIED** |
| 오픈소스 공개 시 **핵심 부분이 공개범위에 반드시 포함** | 세부안내 p.6 "5-다" | - | 참고 |

> **경고**: 규칙 준수를 위해 저장소 이름 변경이 필요할 수 있으나, 사용자 명시 승인 없이 rename 하지 않음 (`MISSING_INPUTS.md` 동일 지시).
> 규칙상 요구 형태 예: `github.com/jinsu1011/2026ESWContest_free_가만있어도SANDI`

## 5. DEMO VIDEO (시연동영상)

| 요구사항 | 공식 근거 | STATUS |
|---|---|---|
| **3분 이내** | 세부안내 p.4 | 콘티만 존재 |
| **화질 720p 이상** | 세부안내 p.5 | - |
| **실제 작품의 시연 및 설명** 포함 | 세부안내 p.5 | - |
| YouTube 업로드 | 세부안내 p.4 | - |
| 업로드 제목 `2026ESWContest_자유공모_가만있어도SANDI_시연동영상` | 세부안내 p.4 | - |
| 보고서에 동영상 링크 삽입 | 세부안내 p.4 | DRAFT: `[최종 시연동영상 URL 입력 필요]` |
| **최종 판정** | | **MISSING (CRITICAL)** |

보유 자료: `03_Evidence/Demo_Materials/SafeNest_3분_시연영상_콘티.pdf` (스토리보드 — 영상 아님).

## 6. COMPETITION INTEGRITY (규정 제10조 · 제12조)

| 규정 | 원문 요지 | SafeNest 적용 |
|---|---|---|
| 제10조 ① | **상용화된 작품은 출품할 수 없다** | 해당 없음 (프로토타입) |
| 제10조 ② | 출품작 저작권은 각 팀이 소유해야 함 | 확인 필요 |
| 제10조 ③ | 순수 창작물이거나 **기존 SW를 개선한 작품**이어야 하며, 기존 SW(오픈소스, 팀이 창작한 타 대회 입상작 포함) 이용 시 **출처·개선점·추가사항을 개발완료보고서에 상세히 기술**해야 함 | **보고서에 OSS/외부 모델·데이터셋 출처 명시 필수** |
| 제10조 ④ | 타 대회 입상작(교내 제외), 저작권 침해, 모방작, **제작 사실이 허위인 경우 심사 제외 / 수상 취소** | **날조 절대 금지의 규정적 근거** |
| 제12조 ⑨ | 출품작이 타인의 저작권·특허권·상표 등을 침해하지 않음을 보장 | 폰트/이미지/데이터셋 확인 |
| 작성안내 항목2 | 저작권 문제 없는 **서체 및 이미지** 사용 권장, 모든 책임은 참가팀 | macOS 기본 한글 폰트 사용, 폰트 파일 재배포 없음 |

> 주의: 중간계획서는 **제5회 창의혁신 공모전** 제출본(`CANDIDATE_AUDIT.md`). 규정 제10조 ④의 "타 대회 입상작"은 *입상작*에 한하며 중간계획서는 계획서이나, 동일 과제의 타 공모전 이력은 사실대로만 기술해야 함.

## 7. TEAM RULES (자유공모 세부안내 p.2)

| 규칙 | 가만있어도SANDI 적용 | STATUS |
|---|---|---|
| 팀 구성 1~5인 (팀장 포함) | 4인 확인 (김진수/유승하/김태균/한준우/강유나 → 실제 인원 확인 필요) | **NOT VERIFIED** |
| 팀명 20Byte 이내 (한글 10글자) | "가만있어도SANDI" = 한글 5 + 영문 5 → 10+5 = **15 Byte** | PASS |
| 띄어쓰기·특수문자·기호·"테스트"/"TEST" 불가 | 없음 | PASS |
| 영문 사용 시 **대문자만** | "SANDI" 전부 대문자 | PASS |
| 팀명 끝에 '팀' 금지 | 없음 | PASS |
| 참가신청서 기재 + 개인정보 동의한 팀원만 참가자 인정 | 미확인 | **NOT VERIFIED** |

## 8. CURRENT STATUS SUMMARY

| 항목 | STATUS |
|---|---|
| 개발완료보고서 DRAFT (PPTX/PDF) | 본 작업에서 생성 |
| 20p 이내 준수 | 계획 PASS |
| 공식 7개 필수 항목 | 계획 PASS |
| 공식 파일명 규칙 | DRAFT 접미사 사용 (최종 아님) |
| 소스코드 URL 삽입 | PASS (실제 URL) |
| GitHub 저장소 명명 규칙 | **MISSING / NONCOMPLIANT** |
| GitHub Public 여부 | **NOT VERIFIED** |
| OSS 라이선스 감사 | **NOT VERIFIED** |
| 시연동영상 | **MISSING (CRITICAL)** |
| 참가신청서 | **NOT VERIFIED** |
| 팀번호 | **NOT VERIFIED** |
| 표지 | 계획 PASS |
