jinsu1011/safenest-embedded-competition/final-report/docs/07_MISSING_EVIDENCE_PRIORITY.md

# 07_MISSING_EVIDENCE_PRIORITY

## CRITICAL — 제출 자체가 불가능하거나 심사 제외 위험

| # | 결손 | 영향 심사항목 | 영향 페이지 | 필요한 것 | 절차 | 공수 | DRAFT 진행 가능? |
|---|---|---|---|---|---|---|---|
| C-1 | **시연동영상 부재** | 예선 필수 제출물 | 3 | 3분 이내·720p 이상, 실제 작품 시연+설명, YouTube 업로드 제목 `2026ESWContest_자유공모_가만있어도SANDI_시연동영상` | 콘티(`SafeNest_3분_시연영상_콘티.pdf`) 기반 촬영 → 업로드 → URL을 3페이지에 삽입 | HIGH | ✅ (플레이스홀더) |
| C-2 | **GitHub 저장소 명명 규칙 위반** | 제출 규격 (불이익 명시) | 3 | `github.com/jinsu1011/2026ESWContest_free_가만있어도SANDI` 형태 | **사용자 승인 후** rename 또는 신규 공개 저장소 생성 | LOW | ✅ |
| C-3 | **팀번호 미확인** | 표지·파일명 | 표지 | 사무국 배정 팀번호 | 참가신청/구글폼 확인 | LOW | ✅ (`[팀번호 확인 필요]`) |
| C-4 | **강유나 작업 브랜치 미병합** | 팀 역량 10 · 기술성 30 | 6, 11, 20 | `yuname121/integration` @ `9e4ddfe…`를 정본에 병합하거나, 정본 기준으로 기여 재정의 | 팀장 결정 → PR → 정본 재스냅샷 | MEDIUM | ✅ (정본 기준 기술) |

## HIGH — 점수에 직접 타격

| # | 결손 | 영향 | 페이지 | 필요한 것 | 절차 | 공수 |
|---|---|---|---|---|---|---|
| H-1 | **4센서 동시 수신 실기기 로그** | 기술성/완성도 (최대 감점 요인) | 5, 7, 11, 16 | ESP32 시리얼 + Pi `/health`·`/api/state`에서 4채널 `valid` 동시 true인 60초 이상 캡처 | 정본 `.ino` flash → `integration/start_all.sh` → 로그 저장 | MEDIUM |
| H-2 | **통합 HIL (4센서→Risk→경보)** | 기술성 30 | 11, 16 | 4센서 실입력으로 NORMAL→CAUTION→DANGER 전이 + 부저 동작 로그/영상 | 위 H-1 후 시나리오 실행 | HIGH |
| H-3 | **실센서 구동 대시보드/LCD 캡처** | 정보전달력 10 · 완성도 | 11 | 실제 센서값이 표시된 Web·LCD 화면 사진 3종(NORMAL/CAUTION/DANGER) | H-1 상태에서 촬영 | LOW |
| H-4 | **최종 통합 하드웨어 사진** | 독창성·완성도 | 5, 16 | 4센서 + ESP32 + Pi가 하우징에 결합된 완제품 사진 | 3D 출력물 조립 후 촬영 | MEDIUM |
| H-5 | **완성 하우징 실물** | 활용성 20 | 18 | STL 4종 출력·조립 결과 사진 + 체결/공차 확인 | 팀원 출력 담당 | MEDIUM |
| H-6 | **Wi-Fi 절단/복구 시험** | 기술성 | 13 | AP 차단 → ESP32 재접속 → Pi 수신 복구까지의 타임스탬프 로그 | 실기기 1회 시나리오 | LOW |
| H-7 | **공식 통계 원문** (S1, S3) | 독창성 30 (배경 설득력) | 1 | 고용노동부 보도자료 원문 URL·발행일, 산안법 제619조 조문 | 정부 사이트/국가법령정보센터 확인 | LOW |

## MEDIUM

| # | 결손 | 영향 | 페이지 | 필요한 것 | 공수 |
|---|---|---|---|---|---|
| M-1 | Raspberry Pi에서의 **mmWave·CO₂ 모델 추론 지연** | 기술성 | 9 | Pi 5에서 각 모델 벤치마크(열화상은 확보됨) | LOW |
| M-2 | **SDT 데이터셋 라이선스 충돌 해소** | 규정 제10조③④ | 6, 14 | TU Wien/Zenodo 라이선스 원문 확인, 비상업 제한 여부 확정 | LOW |
| M-3 | **CO₂ 임계값 기관 근거** | 활용성·신뢰도 | 10 | 실내공기질 관리법/ASHRAE/KOSHA 등 공식 기준 | LOW |
| M-4 | **CO₂ 센서 분리 60초 원시 로그** | 기술성 (fail-closed 완결) | 8 | SCD40 분리 상태에서 `co2_ppm=null`, `valid.co2=false` 확인 | LOW |
| M-5 | **저장소 LICENSE 파일** | 규정 | — | 최상위 LICENSE 추가 여부 결정 | LOW |
| M-6 | 열화상 **raw→°C 보정 계약** | 기술성 | 9 | 센서별 캘리브레이션 절차 | MEDIUM |
| M-7 | `mr60_20260728_manifest.json` **패키지 누락** | 재현성 | — | 파일 복원 후 `test_mr60_manifest.py` 2건 재실행 | LOW |
| M-8 | **Thermal-44 / Thermal-90 명칭 통일** | 정보전달력 | 5, 9 | 팀 내 정본 명칭 확정 | LOW |

## LOW
데이터시트 원문 6종 · 장시간(≥8h) 전 센서 내구시험 · 다인원/반려동물 시나리오 · PCB · 현장 파일럿 · 원가 산정 근거.

## DRAFT 진행 판단
위 결손에도 **DRAFT PPTX/PDF 생성은 가능**하다. 다만 C-1~C-3이 해소되기 전에는 **최종 제출본으로 승격 불가**.
