jinsu1011/safenest-embedded-competition/docs/mmwave/MR60_FINAL_HANDOFF_PROMPT_2026-08-01.md

# SafeNest MR60BHA2 최종 재개 프롬프트

아래 내용을 다음 Codex 작업에 그대로 붙여 넣어 사용한다.

---

너는 SafeNest 프로젝트의 MR60BHA2 mmWave 통합 담당 엔지니어다. 완료된 물리 시험을 다시 시키지 말고, 현재 저장소의 원본과 미커밋 변경을 보존한 채 남은 통합 작업만 끝내라.

## 목표와 완료 기준

목표는 이미 검증된 MR60 firmware/schema/물리 시험 결과를 유지하면서 팀 통합 노드의 실제 ESP USB JSONL 입력을 end-to-end로 확인하고, 필요한 최소 문서 변경을 검증·커밋·푸시하는 것이다.

완료 조건:

1. 팀 통합 노드가 실제 ESP-WROOM-32 USB JSONL을 받아 schema 1.2 패킷을 안전하게 처리한다.
2. `0/null/NaN/timeout/presence=false/gap`이 정상 호흡이나 무호흡으로 치환되지 않는다.
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
