jinsu1011/safenest-embedded-competition/devices/co2/docs/images/2026-08-12_scd40_module_and_pin_labels.jpg

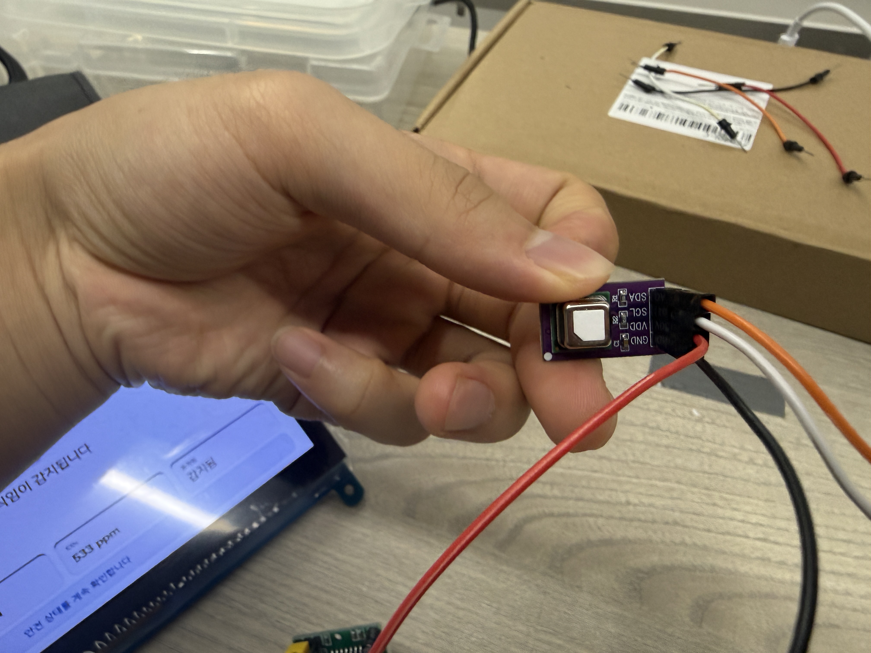
devices/co2/docs/images/2026-08-12_scd40_module_and_pin_labels.jpg
