jinsu1011/safenest-embedded-competition/devices/mmwave/firmware/analysis/hr_sideband/s1_breath_sideband_coupling.png

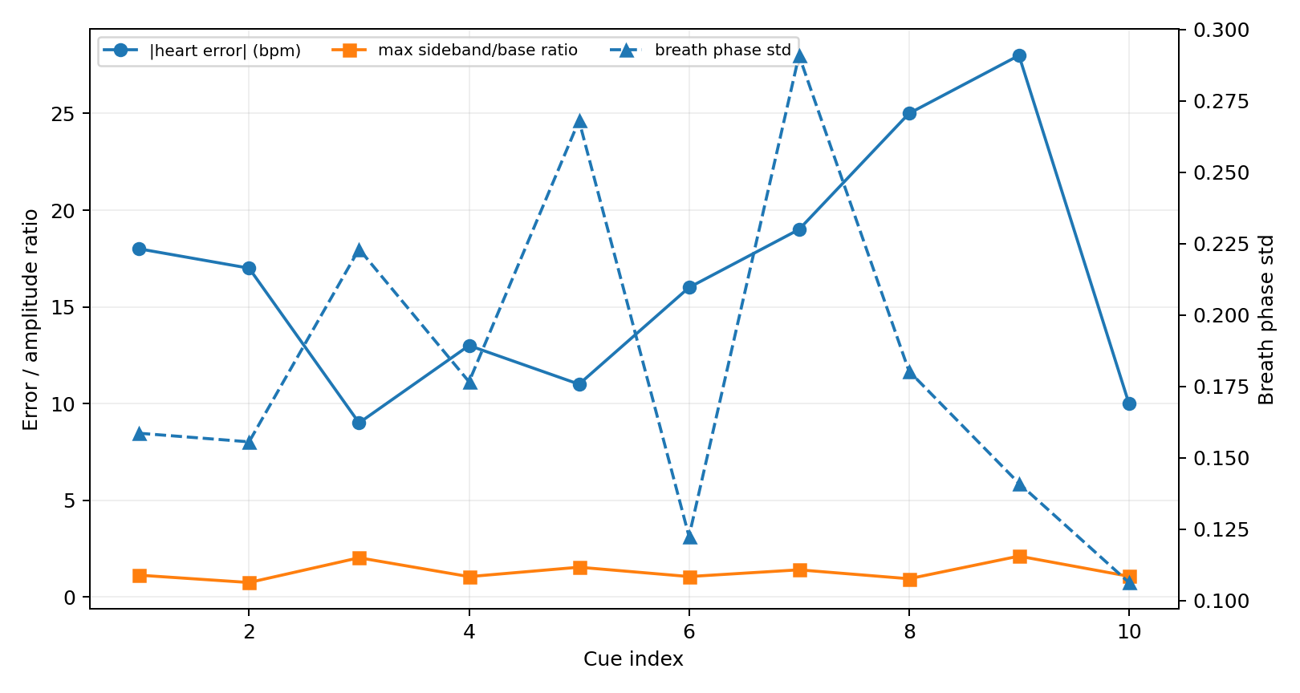
devices/mmwave/firmware/analysis/hr_sideband/s1_breath_sideband_coupling.png
