jinsu1011/safenest-embedded-competition/devices/mmwave/firmware/analysis/hr_sideband/s1_error_vs_respiration.png

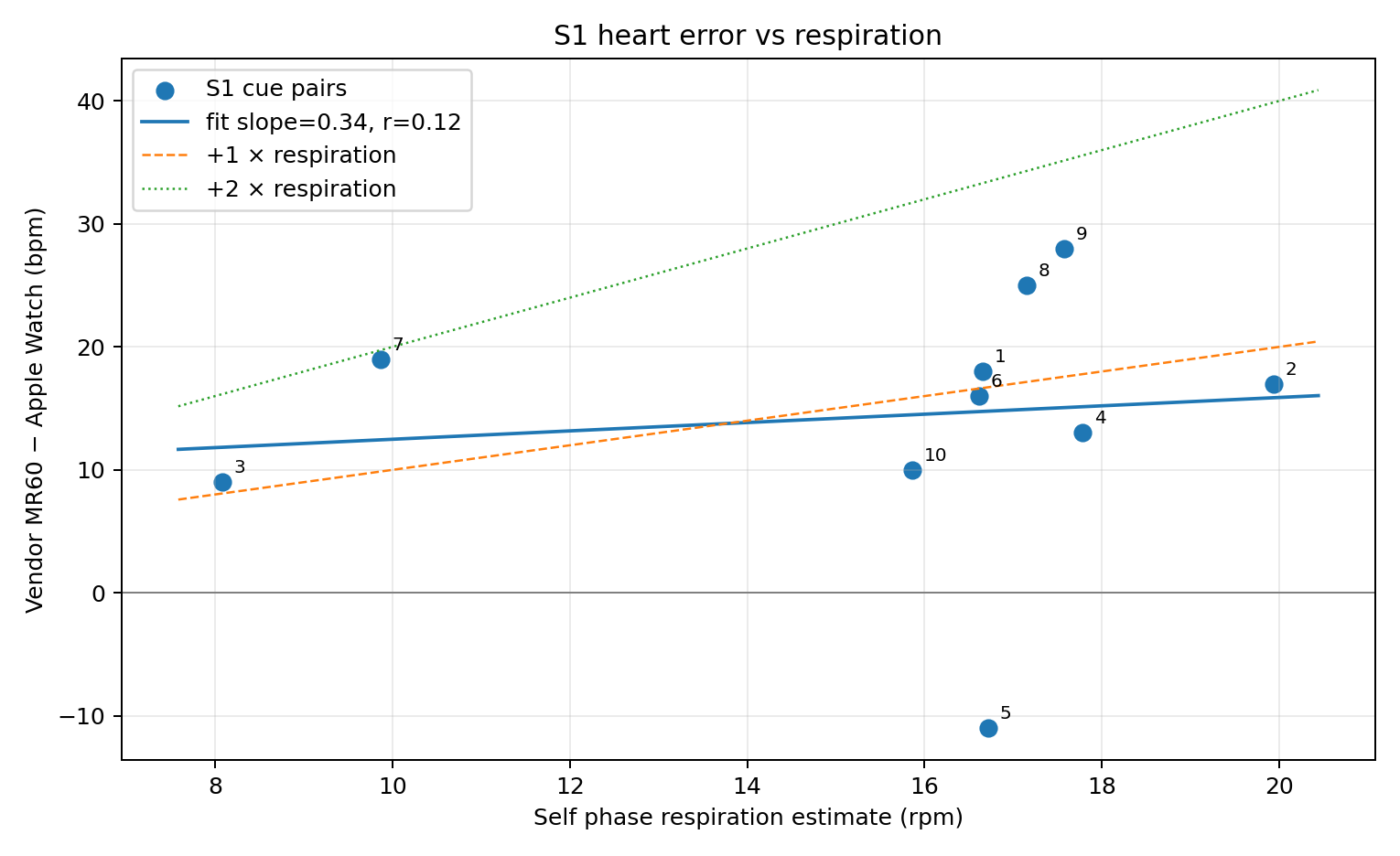
devices/mmwave/firmware/analysis/hr_sideband/s1_error_vs_respiration.png
