jinsu1011/safenest-embedded-competition/devices/mmwave/firmware/analysis/hr_sideband/s1_spectrum_cue_09.png

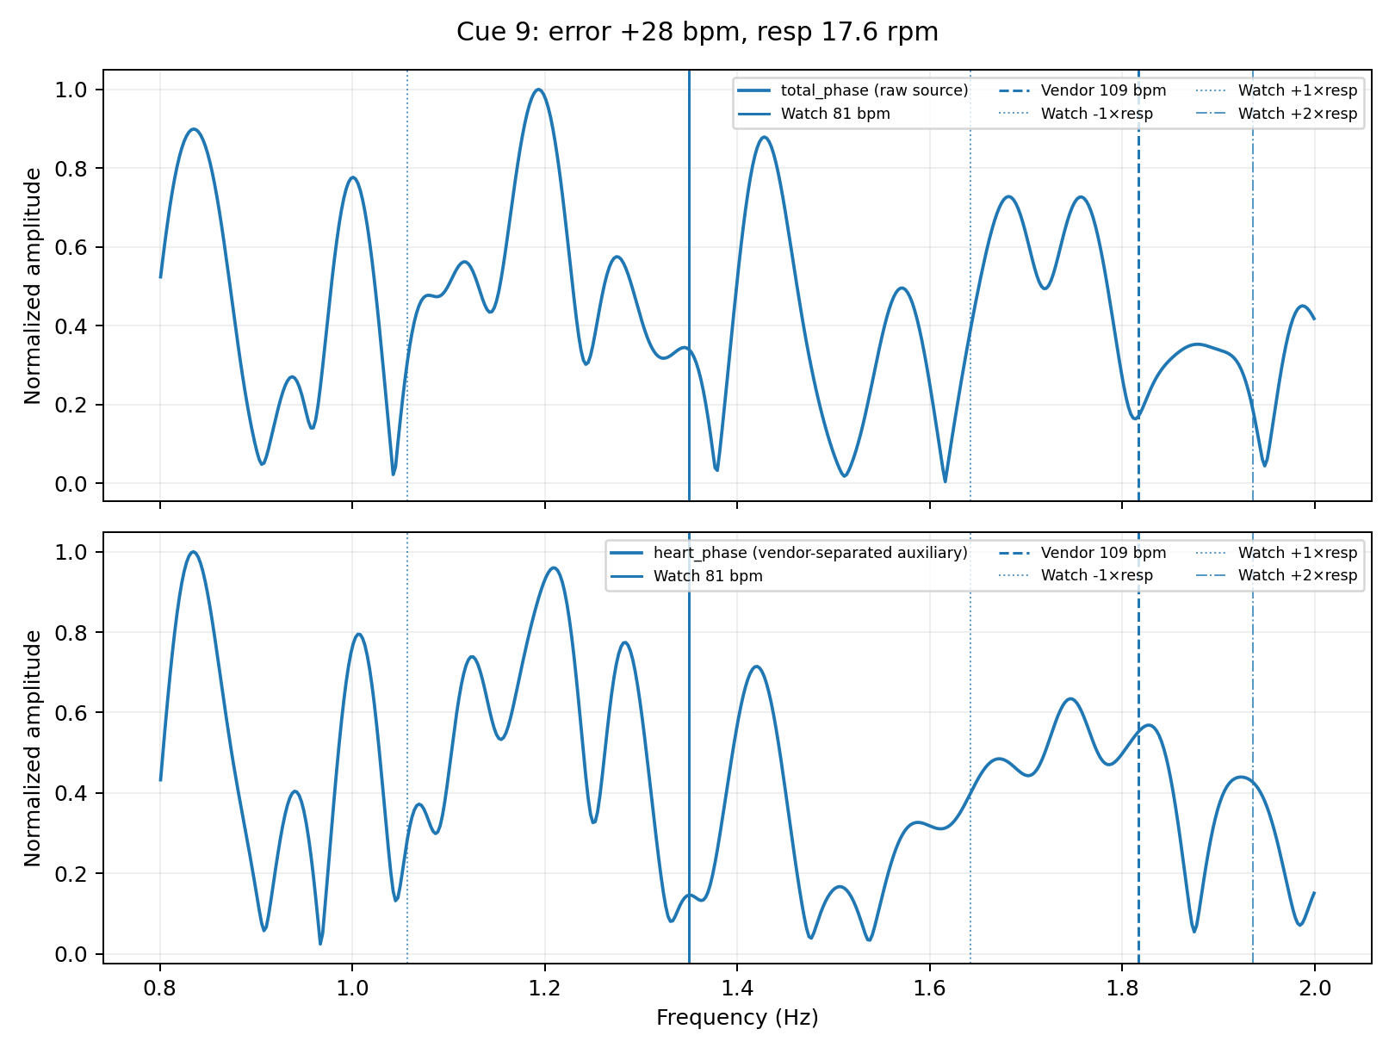
devices/mmwave/firmware/analysis/hr_sideband/s1_spectrum_cue_09.png
