jinsu1011/safenest-embedded-competition/devices/mmwave/firmware/analysis/hr_sideband/s2_recovery_trace.png

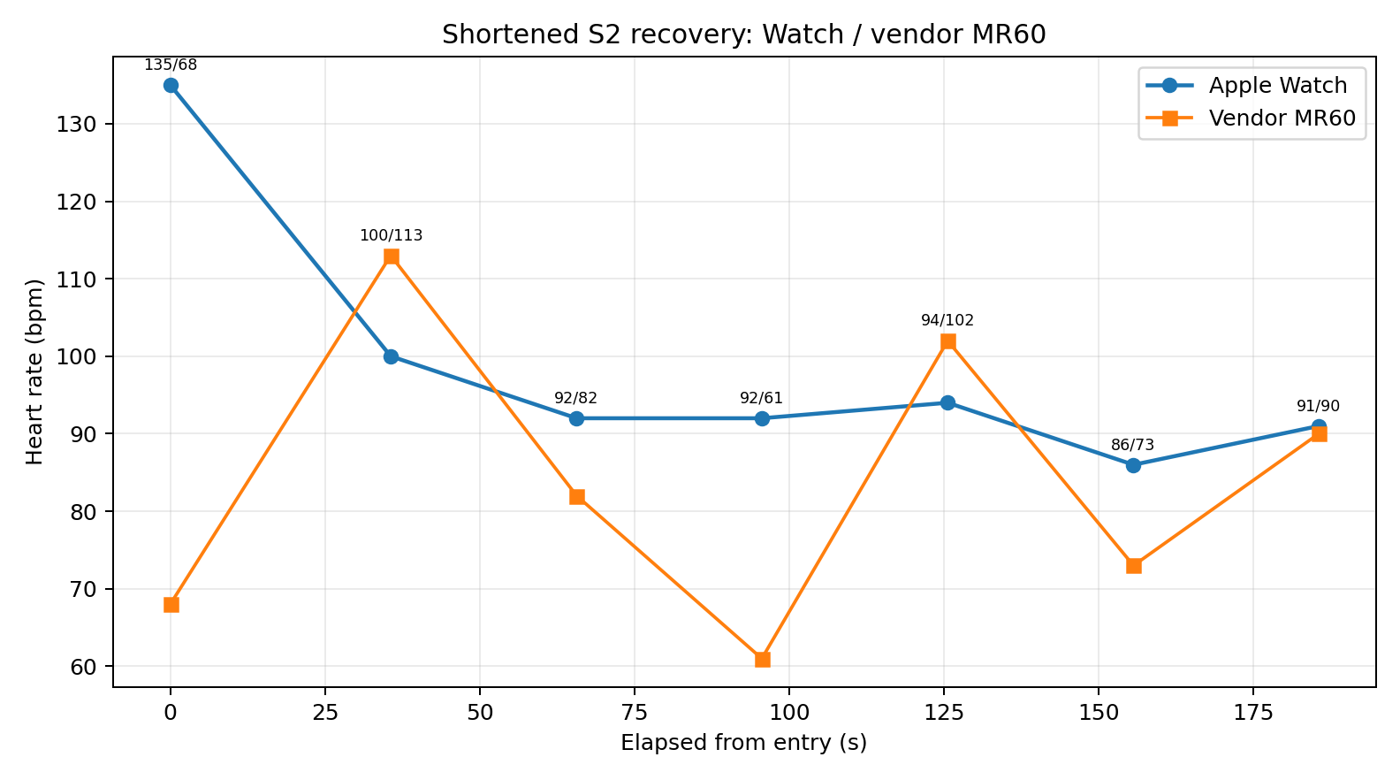
devices/mmwave/firmware/analysis/hr_sideband/s2_recovery_trace.png
