jinsu1011/safenest-embedded-competition/devices/mmwave/firmware/analysis/hr_sideband/s2_spectrum_sample_04.png

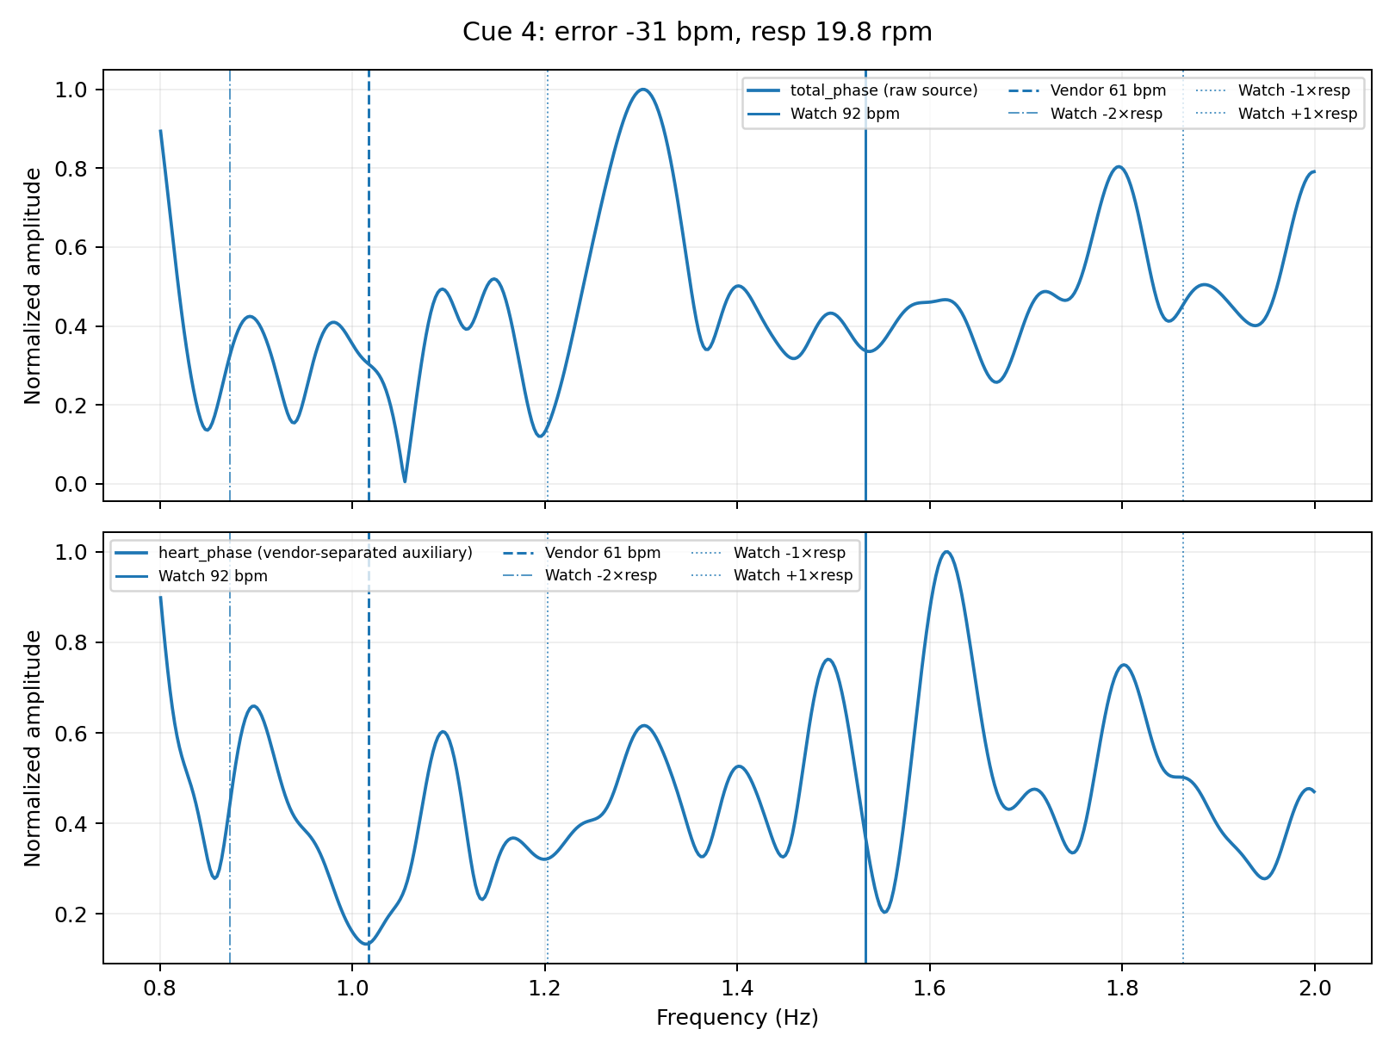
devices/mmwave/firmware/analysis/hr_sideband/s2_spectrum_sample_04.png
