jinsu1011/safenest-embedded-competition/devices/mmwave/firmware/analysis/hr_sideband/s2_time_sync_scan.png

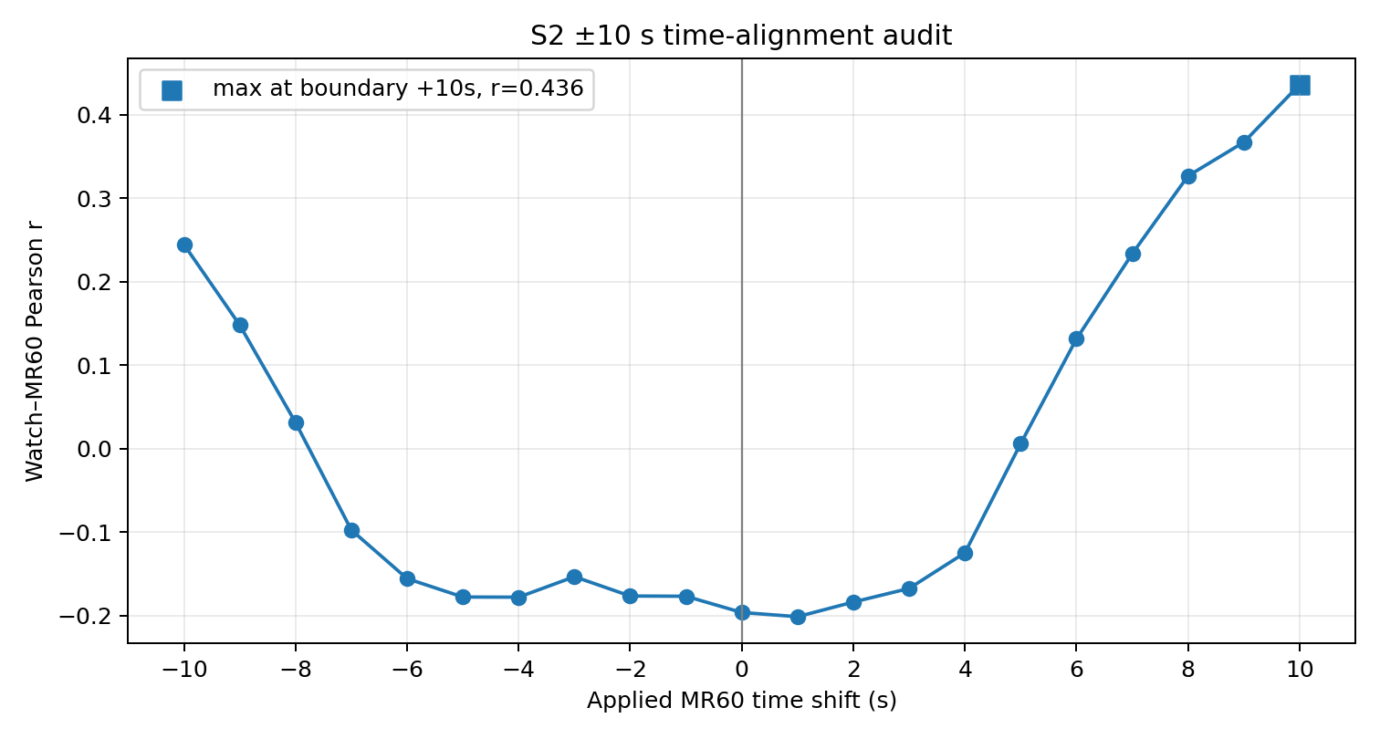
devices/mmwave/firmware/analysis/hr_sideband/s2_time_sync_scan.png
