jinsu1011/safenest-embedded-competition/final-report/assets/3d_trapezoid_T_back_vent.png

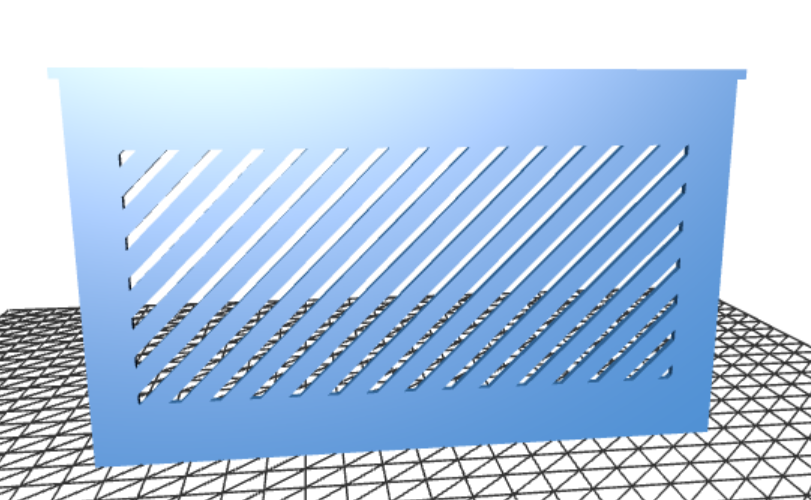
final-report/assets/3d_trapezoid_T_back_vent.png
