jinsu1011/safenest-embedded-competition/final-report/assets/hw_product_full.jpg

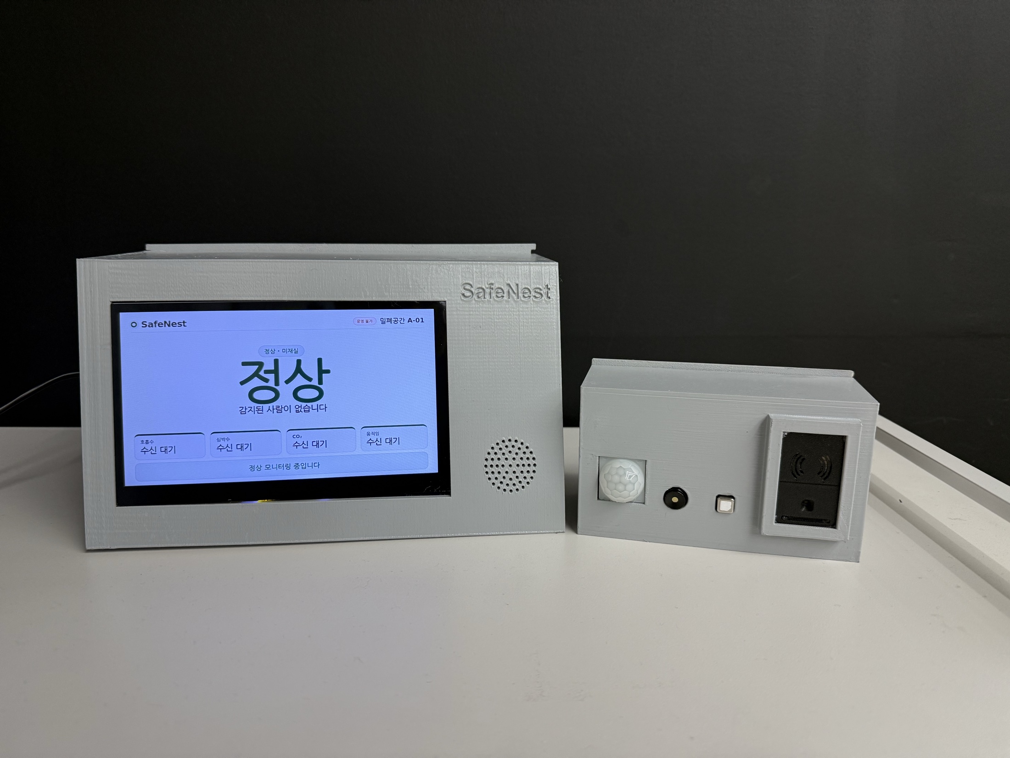
final-report/assets/hw_product_full.jpg
