jinsu1011/safenest-embedded-competition/final-report/assets/ui_lcd_1_normal_empty.jpg

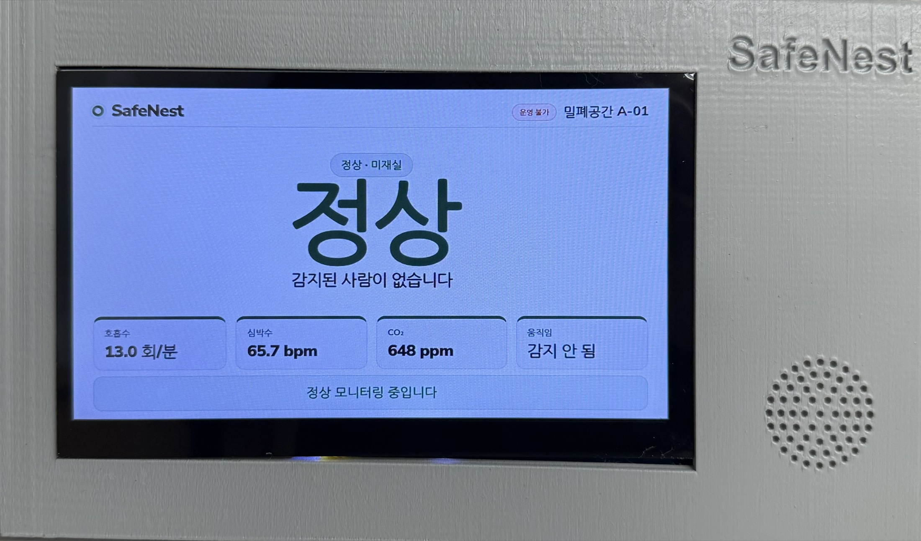
final-report/assets/ui_lcd_1_normal_empty.jpg
