jinsu1011/safenest-embedded-competition/final-report/previews/pdf/p-01.png

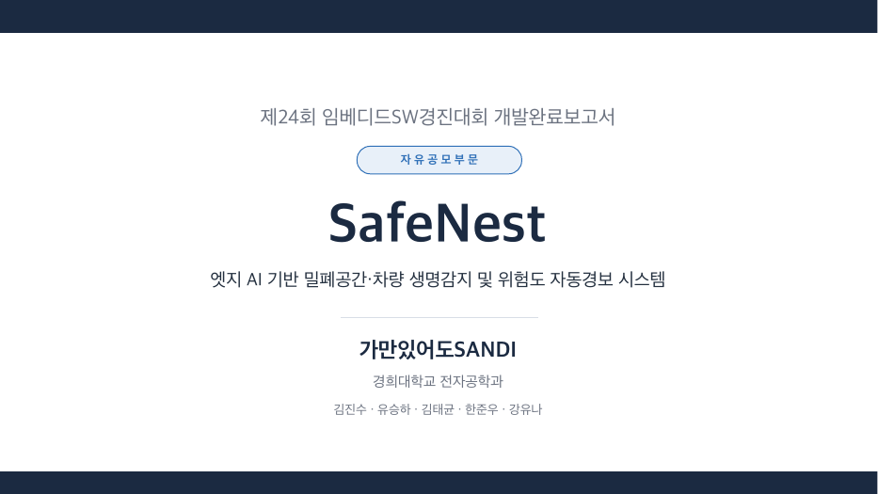
final-report/previews/pdf/p-01.png
