jinsu1011/safenest-embedded-competition/final-report/previews/pdf/p-03.png

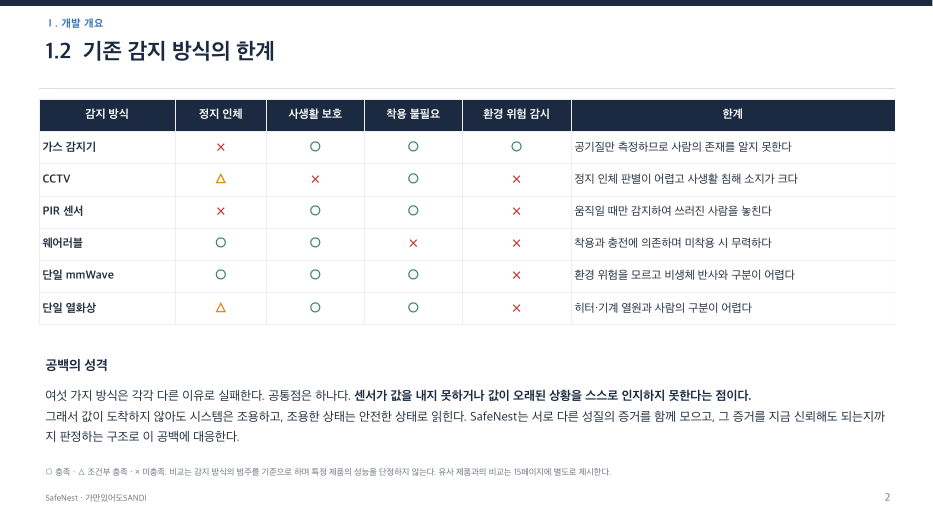
final-report/previews/pdf/p-03.png
