jinsu1011/safenest-embedded-competition/final-report/previews/pdf/p-12.png

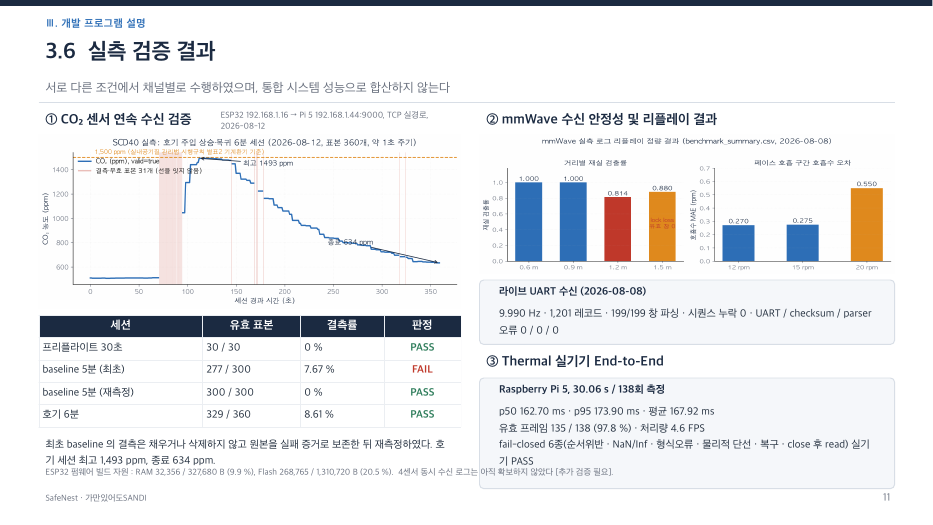
final-report/previews/pdf/p-12.png
