jinsu1011/safenest-embedded-competition/final-report/previews/pdf/p-14.png

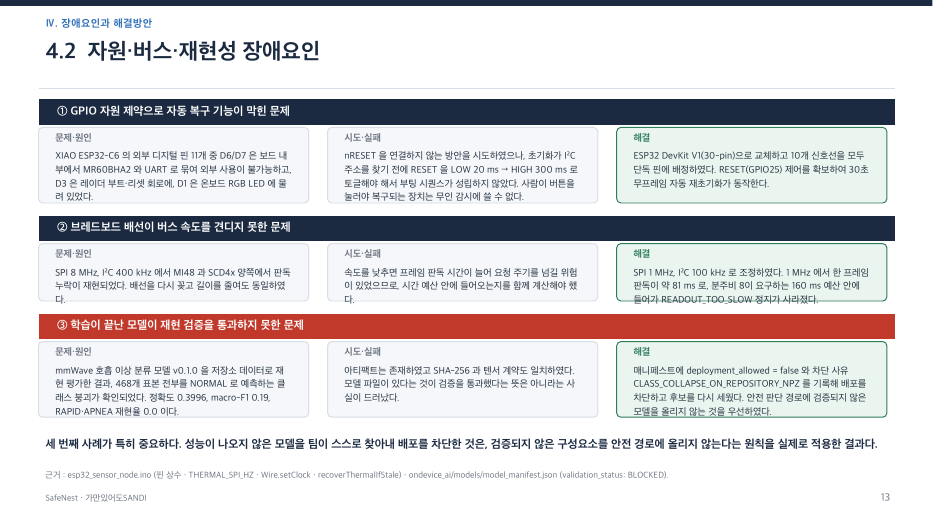
final-report/previews/pdf/p-14.png
