jinsu1011/safenest-embedded-competition/final-report/previews/pdf/p-15.png

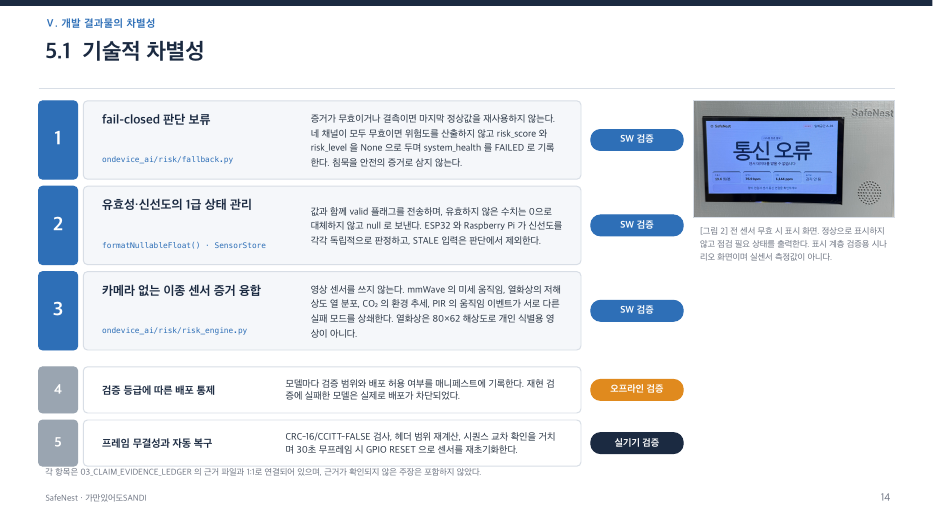
final-report/previews/pdf/p-15.png
