jinsu1011/safenest-embedded-competition/final-report/previews/pdf/p-18.png

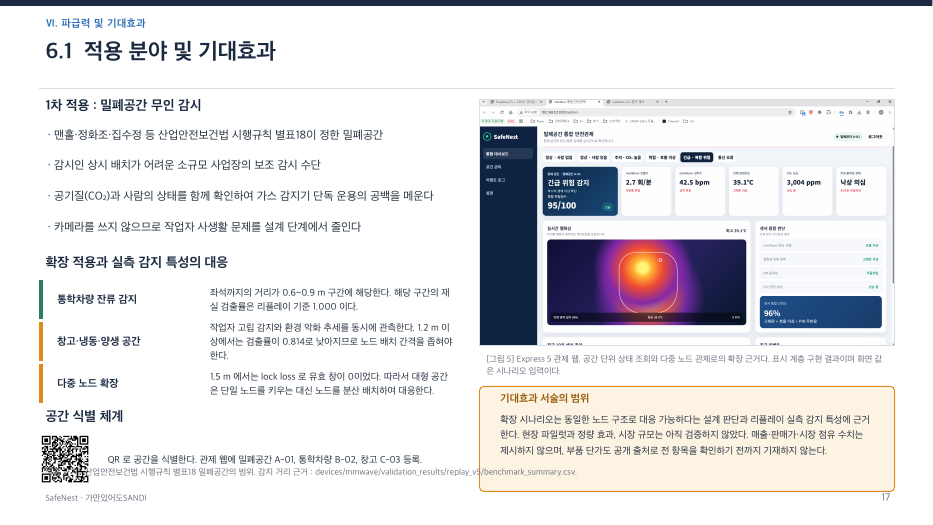
final-report/previews/pdf/p-18.png
