jinsu1011/safenest-embedded-competition/final-report/previews/pdf/p-21.png

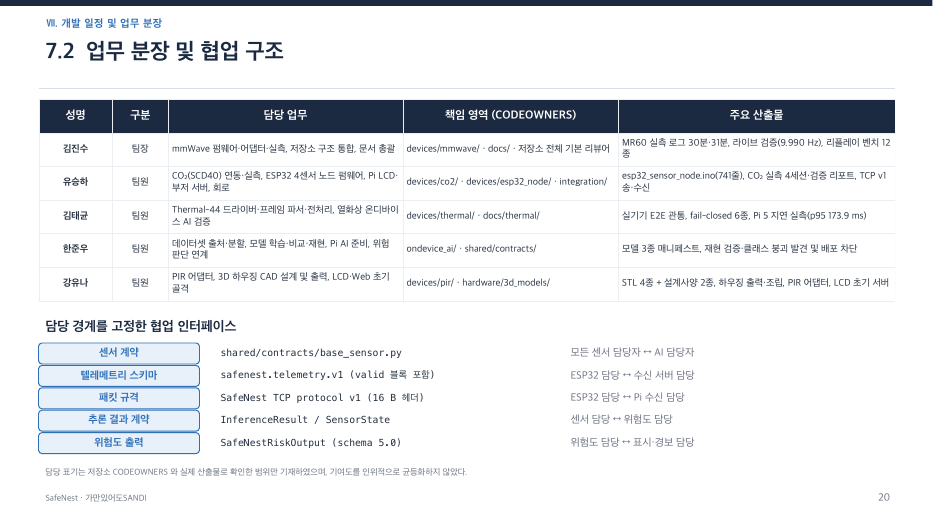
final-report/previews/pdf/p-21.png
