jinsu1011/safenest-embedded-competition/devices/co2/docs/images/2026-08-12_esp32_board_and_wiring.jpg

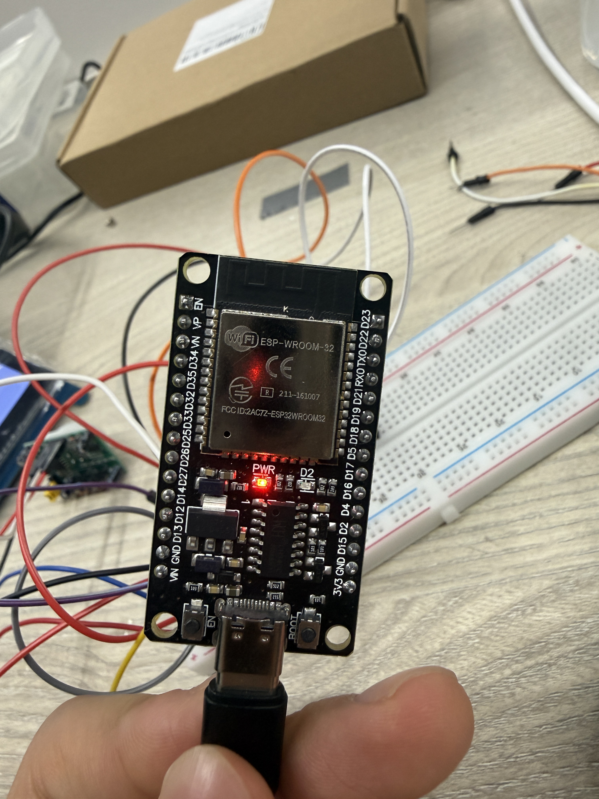
devices/co2/docs/images/2026-08-12_esp32_board_and_wiring.jpg
