jinsu1011/safenest-embedded-competition/ESP32/Arduino/esp32_sensor_node_260828_v2_no_co2_uart1/secrets.h

#pragma once

// Replace these placeholders before uploading to the ESP32.
// ESP32 supports 2.4 GHz Wi-Fi; use the Raspberry Pi's LAN IPv4 address.
constexpr char WIFI_SSID[] = "YOUR_2_4_GHZ_WIFI_SSID";
constexpr char WIFI_PASSWORD[] = "YOUR_WIFI_PASSWORD";
constexpr char RPI_HOST[] = "192.168.1.44";
constexpr uint16_t RPI_PORT = 9000;
