jinsu1011/safenest-embedded-competition/devices/co2/docs/images/2026-08-12_full_sensor_bench.jpg

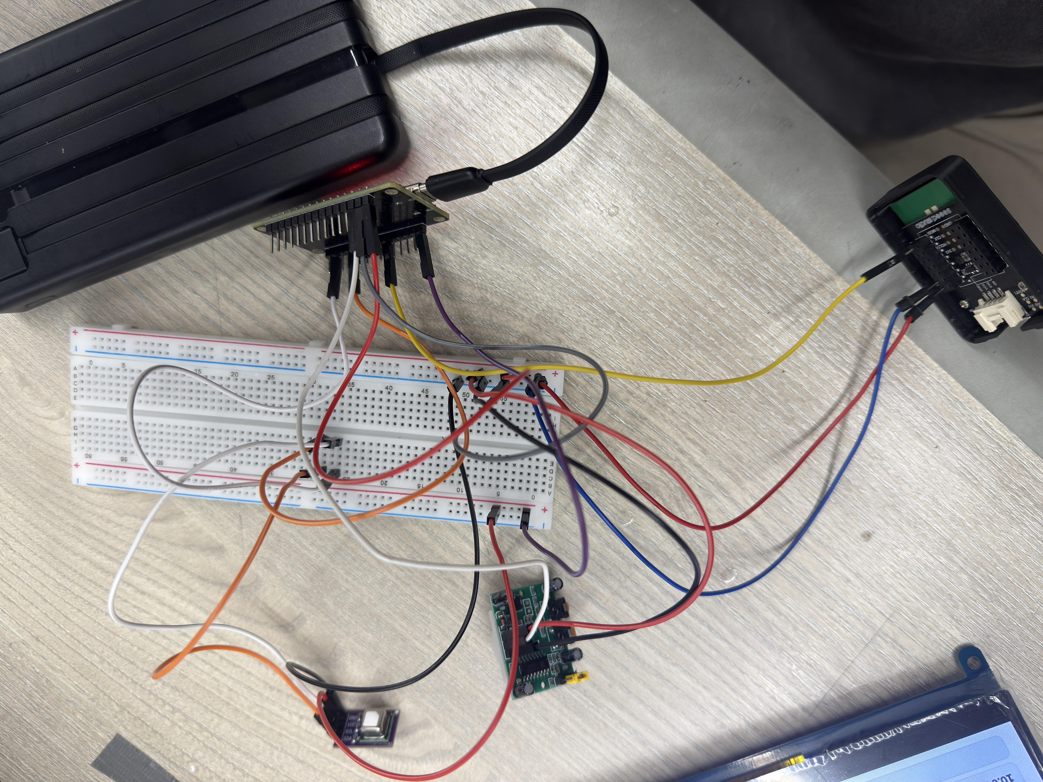
devices/co2/docs/images/2026-08-12_full_sensor_bench.jpg
